The-Ant-Lab/arcobaleno/firmware/build-ARCOBALENO_PLUS/genhdr/pins.h

extern const pin_obj_t pin_A0_obj;
#define pin_A0 (&pin_A0_obj)
extern const pin_af_obj_t pin_A0_af[];
extern const pin_obj_t pin_A1_obj;
#define pin_A1 (&pin_A1_obj)
extern const pin_af_obj_t pin_A1_af[];
extern const pin_obj_t pin_A2_obj;
#define pin_A2 (&pin_A2_obj)
extern const pin_af_obj_t pin_A2_af[];
extern const pin_obj_t pin_A3_obj;
#define pin_A3 (&pin_A3_obj)
extern const pin_af_obj_t pin_A3_af[];
extern const pin_obj_t pin_A4_obj;
#define pin_A4 (&pin_A4_obj)
extern const pin_af_obj_t pin_A4_af[];
extern const pin_obj_t pin_A5_obj;
#define pin_A5 (&pin_A5_obj)
extern const pin_af_obj_t pin_A5_af[];
extern const pin_obj_t pin_A6_obj;
#define pin_A6 (&pin_A6_obj)
extern const pin_af_obj_t pin_A6_af[];
extern const pin_obj_t pin_A7_obj;
#define pin_A7 (&pin_A7_obj)
extern const pin_af_obj_t pin_A7_af[];
extern const pin_obj_t pin_A8_obj;
#define pin_A8 (&pin_A8_obj)
extern const pin_af_obj_t pin_A8_af[];
extern const pin_obj_t pin_A9_obj;
#define pin_A9 (&pin_A9_obj)
extern const pin_af_obj_t pin_A9_af[];
extern const pin_obj_t pin_A10_obj;
#define pin_A10 (&pin_A10_obj)
extern const pin_af_obj_t pin_A10_af[];
extern const pin_obj_t pin_A11_obj;
#define pin_A11 (&pin_A11_obj)
extern const pin_af_obj_t pin_A11_af[];
extern const pin_obj_t pin_A12_obj;
#define pin_A12 (&pin_A12_obj)
extern const pin_af_obj_t pin_A12_af[];
extern const pin_obj_t pin_A15_obj;
#define pin_A15 (&pin_A15_obj)
extern const pin_af_obj_t pin_A15_af[];
extern const pin_obj_t pin_B0_obj;
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
#define pyb_pin_SD_CMD pin_D2
#define pyb_pin_SD_CK pin_C12
#define pyb_pin_SD_SW pin_A15
#define pyb_pin_USB_VBUS pin_A9
#define pyb_pin_USB_DM pin_A11
#define pyb_pin_USB_DP pin_A12
#define pyb_pin_USB_ID pin_A10
#define pyb_pin_OSC32_IN pin_C14
#define pyb_pin_OSC32_OUT pin_C15
