The-Ant-Lab/arcobaleno/firmware/build-ARCOBALENO_PLUS/frozen_content.c

//
// Content for MICROPY_MODULE_FROZEN_STR
//
#include <stdint.h>
const char mp_frozen_str_names[] = {
"\0"};
const uint32_t mp_frozen_str_sizes[] = {
};
const char mp_frozen_str_content[] = {
};
//
// Content for MICROPY_MODULE_FROZEN_MPY
//
#include "py/mpconfig.h"
#include "py/objint.h"
#include "py/objstr.h"
#include "py/emitglue.h"
#include "py/nativeglue.h"

#if MICROPY_OPT_CACHE_MAP_LOOKUP_IN_BYTECODE != 0
#error "incompatible MICROPY_OPT_CACHE_MAP_LOOKUP_IN_BYTECODE"
#endif

#if MICROPY_LONGINT_IMPL != 2
#error "incompatible MICROPY_LONGINT_IMPL"
#endif

#if MPZ_DIG_SIZE != 16
#error "incompatible MPZ_DIG_SIZE"
#endif

#if MICROPY_PY_BUILTINS_FLOAT
typedef struct _mp_obj_float_t {
    mp_obj_base_t base;
    mp_float_t value;
} mp_obj_float_t;
#endif

#if MICROPY_PY_BUILTINS_COMPLEX
typedef struct _mp_obj_complex_t {
    mp_obj_base_t base;
    mp_float_t real;
    mp_float_t imag;
} mp_obj_complex_t;
#endif

enum {
    MP_QSTR_dht_dot_py = MP_QSTRnumber_of,
    MP_QSTR_esp,
    MP_QSTR_DHTBase,
    MP_QSTR_DHT11,
    MP_QSTR_DHT22,
    MP_QSTR_measure,
    MP_QSTR_buf,
    MP_QSTR_humidity,
    MP_QSTR_temperature,
    MP_QSTR_lcd160cr_dot_py,
    MP_QSTR_PORTRAIT,
    MP_QSTR_LANDSCAPE,
    MP_QSTR_PORTRAIT_UPSIDEDOWN,
    MP_QSTR_LANDSCAPE_UPSIDEDOWN,
    MP_QSTR_STARTUP_DECO_NONE,
    MP_QSTR_STARTUP_DECO_MLOGO,
    MP_QSTR_STARTUP_DECO_INFO,
    MP_QSTR__uart_baud_table,
    MP_QSTR_LCD160CR,
    MP_QSTR_pwr,
    MP_QSTR_i2c,
    MP_QSTR_spi,
    MP_QSTR_i2c_addr,
    MP_QSTR__send,
    MP_QSTR__fcmd2,
    MP_QSTR__fcmd2b,
    MP_QSTR__waitfor,
    MP_QSTR_oflush,
    MP_QSTR_iflush,
    MP_QSTR_rgb,
    MP_QSTR_clip_line,
    MP_QSTR_set_power,
    MP_QSTR_set_orient,
    MP_QSTR_set_brightness,
    MP_QSTR_set_i2c_addr,
    MP_QSTR_set_uart_baudrate,
    MP_QSTR_set_startup_deco,
    MP_QSTR_save_to_flash,
    MP_QSTR_set_pixel,
    MP_QSTR_get_pixel,
    MP_QSTR_get_line,
    MP_QSTR_screen_dump,
    MP_QSTR_screen_load,
    MP_QSTR_set_pos,
    MP_QSTR_set_text_color,
    MP_QSTR_set_font,
    MP_QSTR_set_pen,
    MP_QSTR_erase,
    MP_QSTR_dot,
    MP_QSTR_rect_outline,
    MP_QSTR_rect_interior,
    MP_QSTR_dot_no_clip,
    MP_QSTR_rect_no_clip,
    MP_QSTR_rect_outline_no_clip,
    MP_QSTR_rect_interior_no_clip,
    MP_QSTR_line_no_clip,
    MP_QSTR_poly_dot,
    MP_QSTR_poly_line,
    MP_QSTR_touch_config,
    MP_QSTR_is_touched,
    MP_QSTR_get_touch,
    MP_QSTR_set_spi_win,
    MP_QSTR_fast_spi,
    MP_QSTR_show_framebuf,
    MP_QSTR_set_scroll,
    MP_QSTR_set_scroll_win,
    MP_QSTR_set_scroll_win_param,
    MP_QSTR_set_scroll_buf,
    MP_QSTR_jpeg_start,
    MP_QSTR_jpeg_data,
    MP_QSTR_jpeg,
    MP_QSTR_feed_wdt,
    MP_QSTR_X,
    MP_QSTR_Y,
    MP_QSTR_XY,
    MP_QSTR_YX,
    MP_QSTR_4,
    MP_QSTR_C,
    MP_QSTR_buf16,
    MP_QSTR_buf19,
    MP_QSTR_buf1,
    MP_QSTR_array4,
    MP_QSTR__lt_BBBBBB,
    MP_QSTR_w,
    MP_QSTR_h,
    MP_QSTR_cmd,
    MP_QSTR_fmt,
    MP_QSTR_a0,
    MP_QSTR_a1,
    MP_QSTR_a2,
    MP_QSTR_a3,
    MP_QSTR_a4,
    MP_QSTR_n,
    MP_QSTR_g,
    MP_QSTR_c,
    MP_QSTR__lt_BBB,
    MP_QSTR_orient,
    MP_QSTR__lt_BBW,
    MP_QSTR__lt_BBBBH,
    MP_QSTR_x,
    MP_QSTR_y,
    MP_QSTR__lt_BBBB,
    MP_QSTR__lt_BBBBB,
    MP_QSTR__lt_BBHBBB,
    MP_QSTR__lt_BBHH,
    MP_QSTR_fg,
    MP_QSTR_bg,
    MP_QSTR_font,
    MP_QSTR_scale,
    MP_QSTR_bold,
    MP_QSTR_trans,
    MP_QSTR_s,
    MP_QSTR_x1,
    MP_QSTR_y1,
    MP_QSTR_x2,
    MP_QSTR_y2,
    MP_QSTR_calib,
    MP_QSTR_save,
    MP_QSTR_win,
    MP_QSTR_vec,
    MP_QSTR_pat,
    MP_QSTR_color,
    MP_QSTR_param,
    MP_QSTR__lt_BBH,
    MP_QSTR_l,
    MP_QSTR_lcd160cr_test_dot_py,
    MP_QSTR_lcd160cr,
    MP_QSTR_get_lcd,
    MP_QSTR_show_adc,
    MP_QSTR_test_features,
    MP_QSTR_test_mandel,
    MP_QSTR_test_all,
    MP_QSTR_lcd,
    MP_QSTR__percent_4s_colon__space_,
    MP_QSTR_TEMP,
    MP_QSTR_VBAT,
    MP_QSTR__percent_6_dot_3fV,
    MP_QSTR__percent_5_dot_1f_deg_C,
    MP_QSTR_adc,
    MP_QSTR__percent__dot_2f_space_fps,
    MP_QSTR_in_set,
    MP_QSTR_onewire_dot_py,
    MP_QSTR__ow,
    MP_QSTR_OneWireError,
    MP_QSTR_OneWire,
    MP_QSTR_SEARCH_ROM,
    MP_QSTR_MATCH_ROM,
    MP_QSTR_SKIP_ROM,
    MP_QSTR_select_rom,
    MP_QSTR__search_rom,
    MP_QSTR_required,
    MP_QSTR_rom,
    MP_QSTR_l_rom,
    MP_QSTR_diff,
};

extern const qstr_pool_t mp_qstr_const_pool;
const qstr_pool_t mp_qstr_frozen_const_pool = {
    (qstr_pool_t*)&mp_qstr_const_pool, // previous pool
    MP_QSTRnumber_of, // previous pool size
    10, // allocated entries
    154, // used entries
    {
        (const byte*)"\x5a\xdd\x06" "dht.py",
        (const byte*)"\x63\x24\x03" "esp",
        (const byte*)"\x28\x6f\x07" "DHTBase",
        (const byte*)"\x5d\x80\x05" "DHT11",
        (const byte*)"\xfd\x80\x05" "DHT22",
        (const byte*)"\x1d\xae\x07" "measure",
        (const byte*)"\x74\x49\x03" "buf",
        (const byte*)"\x7c\xaf\x08" "humidity",
        (const byte*)"\xe9\xde\x0b" "temperature",
        (const byte*)"\xcf\xa5\x0b" "lcd160cr.py",
        (const byte*)"\xf2\xcd\x08" "PORTRAIT",
        (const byte*)"\xa6\x7b\x09" "LANDSCAPE",
        (const byte*)"\x01\xb5\x13" "PORTRAIT_UPSIDEDOWN",
        (const byte*)"\xd5\x40\x14" "LANDSCAPE_UPSIDEDOWN",
        (const byte*)"\xa7\xaf\x11" "STARTUP_DECO_NONE",
        (const byte*)"\x2b\x04\x12" "STARTUP_DECO_MLOGO",
        (const byte*)"\xc3\x10\x11" "STARTUP_DECO_INFO",
        (const byte*)"\x44\xc8\x10" "_uart_baud_table",
        (const byte*)"\xc8\x0e\x08" "LCD160CR",
        (const byte*)"\x30\x70\x03" "pwr",
        (const byte*)"\x5d\x5f\x03" "i2c",
        (const byte*)"\xcf\x8d\x03" "spi",
        (const byte*)"\x11\x1f\x08" "i2c_addr",
        (const byte*)"\x46\xdc\x05" "_send",
        (const byte*)"\x24\x42\x06" "_fcmd2",
        (const byte*)"\xc6\x86\x07" "_fcmd2b",
        (const byte*)"\xca\x81\x08" "_waitfor",
        (const byte*)"\xce\x08\x06" "oflush",
        (const byte*)"\x08\xd7\x06" "iflush",
        (const byte*)"\xb2\x8a\x03" "rgb",
        (const byte*)"\x22\xd7\x09" "clip_line",
        (const byte*)"\xa7\xfd\x09" "set_power",
        (const byte*)"\xd3\x6a\x0a" "set_orient",
        (const byte*)"\x91\xbe\x0e" "set_brightness",
        (const byte*)"\x8c\xe7\x0c" "set_i2c_addr",
        (const byte*)"\xc5\xd9\x11" "set_uart_baudrate",
        (const byte*)"\x8f\xbe\x10" "set_startup_deco",
        (const byte*)"\x0f\x3f\x0d" "save_to_flash",
        (const byte*)"\xb0\xda\x09" "set_pixel",
        (const byte*)"\xa4\x17\x09" "get_pixel",
        (const byte*)"\x82\x28\x08" "get_line",
        (const byte*)"\x9a\x5d\x0b" "screen_dump",
        (const byte*)"\x10\xea\x0b" "screen_load",
        (const byte*)"\x54\x6d\x07" "set_pos",
        (const byte*)"\x07\xa7\x0e" "set_text_color",
        (const byte*)"\xcb\xd4\x08" "set_font",
        (const byte*)"\x83\x6d\x07" "set_pen",
        (const byte*)"\xe5\x45\x05" "erase",
        (const byte*)"\x3a\x1f\x03" "dot",
        (const byte*)"\xda\x1c\x0c" "rect_outline",
        (const byte*)"\xca\x14\x0d" "rect_interior",
        (const byte*)"\xed\x75\x0b" "dot_no_clip",
        (const byte*)"\x72\x73\x0c" "rect_no_clip",
        (const byte*)"\x8d\x0a\x14" "rect_outline_no_clip",
        (const byte*)"\x9d\x7e\x15" "rect_interior_no_clip",
        (const byte*)"\x5c\x4e\x0c" "line_no_clip",
        (const byte*)"\x6f\x13\x08" "poly_dot",
        (const byte*)"\xfe\x9a\x09" "poly_line",
        (const byte*)"\x15\x99\x0c" "touch_config",
        (const byte*)"\x04\x72\x0a" "is_touched",
        (const byte*)"\x69\xf2\x09" "get_touch",
        (const byte*)"\x9d\x18\x0b" "set_spi_win",
        (const byte*)"\xf0\x3a\x08" "fast_spi",
        (const byte*)"\x75\x65\x0d" "show_framebuf",
        (const byte*)"\x35\xb2\x0a" "set_scroll",
        (const byte*)"\xda\x67\x0e" "set_scroll_win",
        (const byte*)"\x8a\xbd\x14" "set_scroll_win_param",
        (const byte*)"\x1b\x1a\x0e" "set_scroll_buf",
        (const byte*)"\x22\xea\x0a" "jpeg_start",
        (const byte*)"\x52\x10\x09" "jpeg_data",
        (const byte*)"\x7d\xe7\x04" "jpeg",
        (const byte*)"\x3f\x67\x08" "feed_wdt",
        (const byte*)"\xfd\xb5\x01" "X",
        (const byte*)"\xfc\xb5\x01" "Y",
        (const byte*)"\xc4\x75\x02" "XY",
        (const byte*)"\x24\x75\x02" "YX",
        (const byte*)"\x91\xb5\x01" "4",
        (const byte*)"\xe6\xb5\x01" "C",
        (const byte*)"\x53\x70\x05" "buf16",
        (const byte*)"\x5c\x70\x05" "buf19",
        (const byte*)"\xc5\x77\x04" "buf1",
        (const byte*)"\xc8\xc1\x06" "array4",
        (const byte*)"\x19\x0d\x07" "<BBBBBB",
        (const byte*)"\xd2\xb5\x01" "w",
        (const byte*)"\xcd\xb5\x01" "h",
        (const byte*)"\x2f\x4c\x03" "cmd",
        (const byte*)"\x7a\x38\x03" "fmt",
        (const byte*)"\x74\x6e\x02" "a0",
        (const byte*)"\x75\x6e\x02" "a1",
        (const byte*)"\x76\x6e\x02" "a2",
        (const byte*)"\x77\x6e\x02" "a3",
        (const byte*)"\x70\x6e\x02" "a4",
        (const byte*)"\xcb\xb5\x01" "n",
        (const byte*)"\xc2\xb5\x01" "g",
        (const byte*)"\xc6\xb5\x01" "c",
        (const byte*)"\x7b\x8b\x04" "<BBB",
        (const byte*)"\x8e\x81\x06" "orient",
        (const byte*)"\x6e\x8b\x04" "<BBW",
        (const byte*)"\xf1\x4d\x06" "<BBBBH",
        (const byte*)"\xdd\xb5\x01" "x",
        (const byte*)"\xdc\xb5\x01" "y",
        (const byte*)"\x99\xfa\x05" "<BBBB",
        (const byte*)"\xfb\x4d\x06" "<BBBBB",
        (const byte*)"\xd3\xc2\x07" "<BBHBBB",
        (const byte*)"\xd9\xf9\x05" "<BBHH",
        (const byte*)"\x44\x6e\x02" "fg",
        (const byte*)"\xc0\x6e\x02" "bg",
        (const byte*)"\x96\x2b\x04" "font",
        (const byte*)"\x7d\x51\x05" "scale",
        (const byte*)"\x40\x3c\x04" "bold",
        (const byte*)"\x5f\x45\x05" "trans",
        (const byte*)"\xd6\xb5\x01" "s",
        (const byte*)"\x4c\x71\x02" "x1",
        (const byte*)"\x6d\x71\x02" "y1",
        (const byte*)"\x4f\x71\x02" "x2",
        (const byte*)"\x6e\x71\x02" "y2",
        (const byte*)"\xc0\xed\x05" "calib",
        (const byte*)"\xa4\x83\x04" "save",
        (const byte*)"\xb5\x7f\x03" "win",
        (const byte*)"\x75\x7b\x03" "vec",
        (const byte*)"\xe0\x72\x03" "pat",
        (const byte*)"\xd8\x06\x05" "color",
        (const byte*)"\xca\xc8\x05" "param",
        (const byte*)"\x71\x8b\x04" "<BBH",
        (const byte*)"\xc9\xb5\x01" "l",
        (const byte*)"\x46\x96\x10" "lcd160cr_test.py",
        (const byte*)"\xe8\xf0\x08" "lcd160cr",
        (const byte*)"\xc7\x27\x07" "get_lcd",
        (const byte*)"\xdf\x50\x08" "show_adc",
        (const byte*)"\x2b\x6e\x0d" "test_features",
        (const byte*)"\xc3\x88\x0b" "test_mandel",
        (const byte*)"\xad\xc8\x08" "test_all",
        (const byte*)"\xae\x3f\x03" "lcd",
        (const byte*)"\x9d\x48\x05" "%4s: ",
        (const byte*)"\xe9\xd1\x04" "TEMP",
        (const byte*)"\x24\xc4\x04" "VBAT",
        (const byte*)"\x1b\x2a\x06" "%6.3fV",
        (const byte*)"\x7d\x03\x08" "\x25\x35\x2e\x31\x66\xc2\xb0\x43",
        (const byte*)"\x43\x32\x03" "adc",
        (const byte*)"\x7f\x5a\x08" "%.2f fps",
        (const byte*)"\x1f\x11\x06" "in_set",
        (const byte*)"\x0f\xd8\x0a" "onewire.py",
        (const byte*)"\x82\x1f\x03" "_ow",
        (const byte*)"\x50\x5d\x0c" "OneWireError",
        (const byte*)"\x68\xd8\x07" "OneWire",
        (const byte*)"\xa4\x6f\x0a" "SEARCH_ROM",
        (const byte*)"\xb9\x51\x09" "MATCH_ROM",
        (const byte*)"\xcb\x11\x08" "SKIP_ROM",
        (const byte*)"\xe2\x4f\x0a" "select_rom",
        (const byte*)"\xfb\x7e\x0b" "_search_rom",
        (const byte*)"\x2c\x4c\x08" "required",
        (const byte*)"\xb5\x8b\x03" "rom",
        (const byte*)"\x26\xa3\x05" "l_rom",
        (const byte*)"\xc8\xfc\x04" "diff",
    },
};

// frozen bytecode for file dht.py, scope dht__lt_module_gt__DHTBase___init__
STATIC const byte fun_data_dht__lt_module_gt__DHTBase___init__[27] = {
    0x1a, 0x10,
    MP_QSTR___init__ & 0xff, MP_QSTR___init__ >> 8,
    MP_QSTR_dht_dot_py & 0xff, MP_QSTR_dht_dot_py >> 8,
    0x80, 0x0a, 0x25, 0x00,
    0xb1, 
    0xb0, 
    0x18, MP_QSTR_pin & 0xff, MP_QSTR_pin >> 8, 
    0x12, MP_QSTR_bytearray & 0xff, MP_QSTR_bytearray >> 8, 
    0x85, 
    0x34, 0x01, 
    0xb0, 
    0x18, MP_QSTR_buf & 0xff, MP_QSTR_buf >> 8, 
    0x51, 
    0x63, 
};
STATIC const mp_rom_obj_t const_table_data_dht__lt_module_gt__DHTBase___init__[2] = {
    MP_ROM_QSTR(MP_QSTR_self),
    MP_ROM_QSTR(MP_QSTR_pin),
};
STATIC const mp_raw_code_t raw_code_dht__lt_module_gt__DHTBase___init__ = {
    .kind = MP_CODE_BYTECODE,
    .scope_flags = 0x00,
    .n_pos_args = 2,
    .fun_data = fun_data_dht__lt_module_gt__DHTBase___init__,
    .const_table = (mp_uint_t*)const_table_data_dht__lt_module_gt__DHTBase___init__,
    #if MICROPY_PERSISTENT_CODE_SAVE
    .fun_data_len = 27,
    .n_obj = 0,
    .n_raw_code = 0,
    #if MICROPY_PY_SYS_SETTRACE
    .prelude = {
        .n_state = 4,
        .n_exc_stack = 0,
        .scope_flags = 0,
        .n_pos_args = 2,
        .n_kwonly_args = 0,
        .n_def_pos_args = 0,
        .qstr_block_name = MP_QSTR___init__,
        .qstr_source_file = MP_QSTR_dht_dot_py,
        .line_info = fun_data_dht__lt_module_gt__DHTBase___init__ + 0,
        .opcodes = fun_data_dht__lt_module_gt__DHTBase___init__ + 10,
    },
    .line_of_definition = 0,
    #endif
    #if MICROPY_EMIT_MACHINE_CODE
    .prelude_offset = 0,
    .n_qstr = 0,
    .qstr_link = NULL,
    #endif
    #endif
    #if MICROPY_EMIT_MACHINE_CODE
    .type_sig = 0,
    #endif
};

// frozen bytecode for file dht.py, scope dht__lt_module_gt__DHTBase_measure
STATIC const byte fun_data_dht__lt_module_gt__DHTBase_measure[64] = {
    0x21, 0x14,
    MP_QSTR_measure & 0xff, MP_QSTR_measure >> 8,
    MP_QSTR_dht_dot_py & 0xff, MP_QSTR_dht_dot_py >> 8,
    0x80, 0x0e, 0x25, 0x2b, 0x3a, 0x00,
    0xb0, 
    0x13, MP_QSTR_buf & 0xff, MP_QSTR_buf >> 8, 
    0xc1, 
    0x12, MP_QSTR_dht_readinto & 0xff, MP_QSTR_dht_readinto >> 8, 
    0xb0, 
    0x13, MP_QSTR_pin & 0xff, MP_QSTR_pin >> 8, 
    0xb1, 
    0x34, 0x02, 
    0x59, 
    0xb1, 
    0x80, 
    0x55, 
    0xb1, 
    0x81, 
    0x55, 
    0xf2, 
    0xb1, 
    0x82, 
    0x55, 
    0xf2, 
    0xb1, 
    0x83, 
    0x55, 
    0xf2, 
    0x22, 0x81, 0x7f, 
    0xef, 
    0xb1, 
    0x84, 
    0x55, 
    0xdc, 
    0x44, 0x08, 0x80, 
    0x12, MP_QSTR_Exception & 0xff, MP_QSTR_Exception >> 8, 
    0x23, 0x01, 
    0x34, 0x01, 
    0x65, 
    0x51, 
    0x63, 
};
STATIC const mp_obj_str_t const_obj_dht__lt_module_gt__DHTBase_measure_0 = {{&mp_type_str}, 53040, 14, (const byte*)"\x63\x68\x65\x63\x6b\x73\x75\x6d\x20\x65\x72\x72\x6f\x72"};
STATIC const mp_rom_obj_t const_table_data_dht__lt_module_gt__DHTBase_measure[2] = {
    MP_ROM_QSTR(MP_QSTR_self),
    MP_ROM_PTR(&const_obj_dht__lt_module_gt__DHTBase_measure_0),
};
STATIC const mp_raw_code_t raw_code_dht__lt_module_gt__DHTBase_measure = {
    .kind = MP_CODE_BYTECODE,
    .scope_flags = 0x00,
    .n_pos_args = 1,
    .fun_data = fun_data_dht__lt_module_gt__DHTBase_measure,
    .const_table = (mp_uint_t*)const_table_data_dht__lt_module_gt__DHTBase_measure,
    #if MICROPY_PERSISTENT_CODE_SAVE
    .fun_data_len = 64,
    .n_obj = 1,
    .n_raw_code = 0,
    #if MICROPY_PY_SYS_SETTRACE
    .prelude = {
        .n_state = 5,
        .n_exc_stack = 0,
        .scope_flags = 0,
        .n_pos_args = 1,
        .n_kwonly_args = 0,
        .n_def_pos_args = 0,
        .qstr_block_name = MP_QSTR_measure,
        .qstr_source_file = MP_QSTR_dht_dot_py,
        .line_info = fun_data_dht__lt_module_gt__DHTBase_measure + 0,
        .opcodes = fun_data_dht__lt_module_gt__DHTBase_measure + 12,
    },
    .line_of_definition = 0,
    #endif
    #if MICROPY_EMIT_MACHINE_CODE
    .prelude_offset = 0,
    .n_qstr = 0,
    .qstr_link = NULL,
    #endif
    #endif
    #if MICROPY_EMIT_MACHINE_CODE
    .type_sig = 0,
    #endif
};

// frozen bytecode for file dht.py, scope dht__lt_module_gt__DHTBase
STATIC const byte fun_data_dht__lt_module_gt__DHTBase[35] = {
    0x00, 0x12,
    MP_QSTR_DHTBase & 0xff, MP_QSTR_DHTBase >> 8,
    MP_QSTR_dht_dot_py & 0xff, MP_QSTR_dht_dot_py >> 8,
    0x8c, 0x09, 0x65, 0x20, 0x00,
    0x11, MP_QSTR___name__ & 0xff, MP_QSTR___name__ >> 8, 
    0x16, MP_QSTR___module__ & 0xff, MP_QSTR___module__ >> 8, 
    0x10, MP_QSTR_DHTBase & 0xff, MP_QSTR_DHTBase >> 8, 
    0x16, MP_QSTR___qualname__ & 0xff, MP_QSTR___qualname__ >> 8, 
    0x32, 0x00, 
    0x16, MP_QSTR___init__ & 0xff, MP_QSTR___init__ >> 8, 
    0x32, 0x01, 
    0x16, MP_QSTR_measure & 0xff, MP_QSTR_measure >> 8, 
    0x51, 
    0x63, 
};
STATIC const mp_rom_obj_t const_table_data_dht__lt_module_gt__DHTBase[2] = {
    MP_ROM_PTR(&raw_code_dht__lt_module_gt__DHTBase___init__),
    MP_ROM_PTR(&raw_code_dht__lt_module_gt__DHTBase_measure),
};
STATIC const mp_raw_code_t raw_code_dht__lt_module_gt__DHTBase = {
    .kind = MP_CODE_BYTECODE,
    .scope_flags = 0x00,
    .n_pos_args = 0,
    .fun_data = fun_data_dht__lt_module_gt__DHTBase,
    .const_table = (mp_uint_t*)const_table_data_dht__lt_module_gt__DHTBase,
    #if MICROPY_PERSISTENT_CODE_SAVE
    .fun_data_len = 35,
    .n_obj = 0,
    .n_raw_code = 2,
    #if MICROPY_PY_SYS_SETTRACE
    .prelude = {
        .n_state = 1,
        .n_exc_stack = 0,
        .scope_flags = 0,
        .n_pos_args = 0,
        .n_kwonly_args = 0,
        .n_def_pos_args = 0,
        .qstr_block_name = MP_QSTR_DHTBase,
        .qstr_source_file = MP_QSTR_dht_dot_py,
        .line_info = fun_data_dht__lt_module_gt__DHTBase + 0,
        .opcodes = fun_data_dht__lt_module_gt__DHTBase + 11,
    },
    .line_of_definition = 0,
    #endif
    #if MICROPY_EMIT_MACHINE_CODE
    .prelude_offset = 0,
    .n_qstr = 0,
    .qstr_link = NULL,
    #endif
    #endif
    #if MICROPY_EMIT_MACHINE_CODE
    .type_sig = 0,
    #endif
};

// frozen bytecode for file dht.py, scope dht__lt_module_gt__DHT11_humidity
STATIC const byte fun_data_dht__lt_module_gt__DHT11_humidity[16] = {
    0x11, 0x0e,
    MP_QSTR_humidity & 0xff, MP_QSTR_humidity >> 8,
    MP_QSTR_dht_dot_py & 0xff, MP_QSTR_dht_dot_py >> 8,
    0x80, 0x15, 0x00,
    0xb0, 
    0x13, MP_QSTR_buf & 0xff, MP_QSTR_buf >> 8, 
    0x80, 
    0x55, 
    0x63, 
};
STATIC const mp_rom_obj_t const_table_data_dht__lt_module_gt__DHT11_humidity[1] = {
    MP_ROM_QSTR(MP_QSTR_self),
};
STATIC const mp_raw_code_t raw_code_dht__lt_module_gt__DHT11_humidity = {
    .kind = MP_CODE_BYTECODE,
    .scope_flags = 0x00,
    .n_pos_args = 1,
    .fun_data = fun_data_dht__lt_module_gt__DHT11_humidity,
    .const_table = (mp_uint_t*)const_table_data_dht__lt_module_gt__DHT11_humidity,
    #if MICROPY_PERSISTENT_CODE_SAVE
    .fun_data_len = 16,
    .n_obj = 0,
    .n_raw_code = 0,
    #if MICROPY_PY_SYS_SETTRACE
    .prelude = {
        .n_state = 3,
        .n_exc_stack = 0,
        .scope_flags = 0,
        .n_pos_args = 1,
        .n_kwonly_args = 0,
        .n_def_pos_args = 0,
        .qstr_block_name = MP_QSTR_humidity,
        .qstr_source_file = MP_QSTR_dht_dot_py,
        .line_info = fun_data_dht__lt_module_gt__DHT11_humidity + 0,
        .opcodes = fun_data_dht__lt_module_gt__DHT11_humidity + 9,
    },
    .line_of_definition = 0,
    #endif
    #if MICROPY_EMIT_MACHINE_CODE
    .prelude_offset = 0,
    .n_qstr = 0,
    .qstr_link = NULL,
    #endif
    #endif
    #if MICROPY_EMIT_MACHINE_CODE
    .type_sig = 0,
    #endif
};

// frozen bytecode for file dht.py, scope dht__lt_module_gt__DHT11_temperature
STATIC const byte fun_data_dht__lt_module_gt__DHT11_temperature[16] = {
    0x11, 0x0e,
    MP_QSTR_temperature & 0xff, MP_QSTR_temperature >> 8,
    MP_QSTR_dht_dot_py & 0xff, MP_QSTR_dht_dot_py >> 8,
    0x80, 0x18, 0x00,
    0xb0, 
    0x13, MP_QSTR_buf & 0xff, MP_QSTR_buf >> 8, 
    0x82, 
    0x55, 
    0x63, 
};
STATIC const mp_rom_obj_t const_table_data_dht__lt_module_gt__DHT11_temperature[1] = {
    MP_ROM_QSTR(MP_QSTR_self),
};
STATIC const mp_raw_code_t raw_code_dht__lt_module_gt__DHT11_temperature = {
    .kind = MP_CODE_BYTECODE,
    .scope_flags = 0x00,
    .n_pos_args = 1,
    .fun_data = fun_data_dht__lt_module_gt__DHT11_temperature,
    .const_table = (mp_uint_t*)const_table_data_dht__lt_module_gt__DHT11_temperature,
    #if MICROPY_PERSISTENT_CODE_SAVE
    .fun_data_len = 16,
    .n_obj = 0,
    .n_raw_code = 0,
    #if MICROPY_PY_SYS_SETTRACE
    .prelude = {
        .n_state = 3,
        .n_exc_stack = 0,
        .scope_flags = 0,
        .n_pos_args = 1,
        .n_kwonly_args = 0,
        .n_def_pos_args = 0,
        .qstr_block_name = MP_QSTR_temperature,
        .qstr_source_file = MP_QSTR_dht_dot_py,
        .line_info = fun_data_dht__lt_module_gt__DHT11_temperature + 0,
        .opcodes = fun_data_dht__lt_module_gt__DHT11_temperature + 9,
    },
    .line_of_definition = 0,
    #endif
    #if MICROPY_EMIT_MACHINE_CODE
    .prelude_offset = 0,
    .n_qstr = 0,
    .qstr_link = NULL,
    #endif
    #endif
    #if MICROPY_EMIT_MACHINE_CODE
    .type_sig = 0,
    #endif
};

// frozen bytecode for file dht.py, scope dht__lt_module_gt__DHT11
STATIC const byte fun_data_dht__lt_module_gt__DHT11[34] = {
    0x00, 0x10,
    MP_QSTR_DHT11 & 0xff, MP_QSTR_DHT11 >> 8,
    MP_QSTR_dht_dot_py & 0xff, MP_QSTR_dht_dot_py >> 8,
    0x8c, 0x14, 0x65, 0x00,
    0x11, MP_QSTR___name__ & 0xff, MP_QSTR___name__ >> 8, 
    0x16, MP_QSTR___module__ & 0xff, MP_QSTR___module__ >> 8, 
    0x10, MP_QSTR_DHT11 & 0xff, MP_QSTR_DHT11 >> 8, 
    0x16, MP_QSTR___qualname__ & 0xff, MP_QSTR___qualname__ >> 8, 
    0x32, 0x00, 
    0x16, MP_QSTR_humidity & 0xff, MP_QSTR_humidity >> 8, 
    0x32, 0x01, 
    0x16, MP_QSTR_temperature & 0xff, MP_QSTR_temperature >> 8, 
    0x51, 
    0x63, 
};
STATIC const mp_rom_obj_t const_table_data_dht__lt_module_gt__DHT11[2] = {
    MP_ROM_PTR(&raw_code_dht__lt_module_gt__DHT11_humidity),
    MP_ROM_PTR(&raw_code_dht__lt_module_gt__DHT11_temperature),
};
STATIC const mp_raw_code_t raw_code_dht__lt_module_gt__DHT11 = {
    .kind = MP_CODE_BYTECODE,
    .scope_flags = 0x00,
    .n_pos_args = 0,
    .fun_data = fun_data_dht__lt_module_gt__DHT11,
    .const_table = (mp_uint_t*)const_table_data_dht__lt_module_gt__DHT11,
    #if MICROPY_PERSISTENT_CODE_SAVE
    .fun_data_len = 34,
    .n_obj = 0,
    .n_raw_code = 2,
    #if MICROPY_PY_SYS_SETTRACE
    .prelude = {
        .n_state = 1,
        .n_exc_stack = 0,
        .scope_flags = 0,
        .n_pos_args = 0,
        .n_kwonly_args = 0,
        .n_def_pos_args = 0,
        .qstr_block_name = MP_QSTR_DHT11,
        .qstr_source_file = MP_QSTR_dht_dot_py,
        .line_info = fun_data_dht__lt_module_gt__DHT11 + 0,
        .opcodes = fun_data_dht__lt_module_gt__DHT11 + 10,
    },
    .line_of_definition = 0,
    #endif
    #if MICROPY_EMIT_MACHINE_CODE
    .prelude_offset = 0,
    .n_qstr = 0,
    .qstr_link = NULL,
    #endif
    #endif
    #if MICROPY_EMIT_MACHINE_CODE
    .type_sig = 0,
    #endif
};

// frozen bytecode for file dht.py, scope dht__lt_module_gt__DHT22_humidity
STATIC const byte fun_data_dht__lt_module_gt__DHT22_humidity[28] = {
    0x19, 0x0e,
    MP_QSTR_humidity & 0xff, MP_QSTR_humidity >> 8,
    MP_QSTR_dht_dot_py & 0xff, MP_QSTR_dht_dot_py >> 8,
    0x80, 0x1c, 0x00,
    0xb0, 
    0x13, MP_QSTR_buf & 0xff, MP_QSTR_buf >> 8, 
    0x80, 
    0x55, 
    0x88, 
    0xf0, 
    0xb0, 
    0x13, MP_QSTR_buf & 0xff, MP_QSTR_buf >> 8, 
    0x81, 
    0x55, 
    0xed, 
    0x23, 0x01, 
    0xf4, 
    0x63, 
};
#if MICROPY_OBJ_REPR == MICROPY_OBJ_REPR_A || MICROPY_OBJ_REPR == MICROPY_OBJ_REPR_B
STATIC const mp_obj_float_t const_obj_dht__lt_module_gt__DHT22_humidity_0 = {{&mp_type_float}, 0.1};
#endif
STATIC const mp_rom_obj_t const_table_data_dht__lt_module_gt__DHT22_humidity[2] = {
    MP_ROM_QSTR(MP_QSTR_self),
#if MICROPY_OBJ_REPR == MICROPY_OBJ_REPR_A || MICROPY_OBJ_REPR == MICROPY_OBJ_REPR_B
    MP_ROM_PTR(&const_obj_dht__lt_module_gt__DHT22_humidity_0),
#elif MICROPY_OBJ_REPR == MICROPY_OBJ_REPR_C
    (mp_rom_obj_t)(0xbe4cccce),
#elif MICROPY_OBJ_REPR == MICROPY_OBJ_REPR_D
    (mp_rom_obj_t)(0xbfbd99999999999a),
#endif
};
STATIC const mp_raw_code_t raw_code_dht__lt_module_gt__DHT22_humidity = {
    .kind = MP_CODE_BYTECODE,
    .scope_flags = 0x00,
    .n_pos_args = 1,
    .fun_data = fun_data_dht__lt_module_gt__DHT22_humidity,
    .const_table = (mp_uint_t*)const_table_data_dht__lt_module_gt__DHT22_humidity,
    #if MICROPY_PERSISTENT_CODE_SAVE
    .fun_data_len = 28,
    .n_obj = 1,
    .n_raw_code = 0,
    #if MICROPY_PY_SYS_SETTRACE
    .prelude = {
        .n_state = 4,
        .n_exc_stack = 0,
        .scope_flags = 0,
        .n_pos_args = 1,
        .n_kwonly_args = 0,
        .n_def_pos_args = 0,
        .qstr_block_name = MP_QSTR_humidity,
        .qstr_source_file = MP_QSTR_dht_dot_py,
        .line_info = fun_data_dht__lt_module_gt__DHT22_humidity + 0,
        .opcodes = fun_data_dht__lt_module_gt__DHT22_humidity + 9,
    },
    .line_of_definition = 0,
    #endif
    #if MICROPY_EMIT_MACHINE_CODE
    .prelude_offset = 0,
    .n_qstr = 0,
    .qstr_link = NULL,
    #endif
    #endif
    #if MICROPY_EMIT_MACHINE_CODE
    .type_sig = 0,
    #endif
};

// frozen bytecode for file dht.py, scope dht__lt_module_gt__DHT22_temperature
STATIC const byte fun_data_dht__lt_module_gt__DHT22_temperature[53] = {
    0x21, 0x14,
    MP_QSTR_temperature & 0xff, MP_QSTR_temperature >> 8,
    MP_QSTR_dht_dot_py & 0xff, MP_QSTR_dht_dot_py >> 8,
    0x80, 0x1f, 0x37, 0x2d, 0x23, 0x00,
    0xb0, 
    0x13, MP_QSTR_buf & 0xff, MP_QSTR_buf >> 8, 
    0x82, 
    0x55, 
    0x22, 0x80, 0x7f, 
    0xef, 
    0x88, 
    0xf0, 
    0xb0, 
    0x13, MP_QSTR_buf & 0xff, MP_QSTR_buf >> 8, 
    0x83, 
    0x55, 
    0xed, 
    0x23, 0x01, 
    0xf4, 
    0xc1, 
    0xb0, 
    0x13, MP_QSTR_buf & 0xff, MP_QSTR_buf >> 8, 
    0x82, 
    0x55, 
    0x22, 0x81, 0x00, 
    0xef, 
    0x44, 0x03, 0x80, 
    0xb1, 
    0xd1, 
    0xc1, 
    0xb1, 
    0x63, 
};
#if MICROPY_OBJ_REPR == MICROPY_OBJ_REPR_A || MICROPY_OBJ_REPR == MICROPY_OBJ_REPR_B
STATIC const mp_obj_float_t const_obj_dht__lt_module_gt__DHT22_temperature_0 = {{&mp_type_float}, 0.1};
#endif
STATIC const mp_rom_obj_t const_table_data_dht__lt_module_gt__DHT22_temperature[2] = {
    MP_ROM_QSTR(MP_QSTR_self),
#if MICROPY_OBJ_REPR == MICROPY_OBJ_REPR_A || MICROPY_OBJ_REPR == MICROPY_OBJ_REPR_B
    MP_ROM_PTR(&const_obj_dht__lt_module_gt__DHT22_temperature_0),
#elif MICROPY_OBJ_REPR == MICROPY_OBJ_REPR_C
    (mp_rom_obj_t)(0xbe4cccce),
#elif MICROPY_OBJ_REPR == MICROPY_OBJ_REPR_D
    (mp_rom_obj_t)(0xbfbd99999999999a),
#endif
};
STATIC const mp_raw_code_t raw_code_dht__lt_module_gt__DHT22_temperature = {
    .kind = MP_CODE_BYTECODE,
    .scope_flags = 0x00,
    .n_pos_args = 1,
    .fun_data = fun_data_dht__lt_module_gt__DHT22_temperature,
    .const_table = (mp_uint_t*)const_table_data_dht__lt_module_gt__DHT22_temperature,
    #if MICROPY_PERSISTENT_CODE_SAVE
    .fun_data_len = 53,
    .n_obj = 1,
    .n_raw_code = 0,
    #if MICROPY_PY_SYS_SETTRACE
    .prelude = {
        .n_state = 5,
        .n_exc_stack = 0,
        .scope_flags = 0,
        .n_pos_args = 1,
        .n_kwonly_args = 0,
        .n_def_pos_args = 0,
        .qstr_block_name = MP_QSTR_temperature,
        .qstr_source_file = MP_QSTR_dht_dot_py,
        .line_info = fun_data_dht__lt_module_gt__DHT22_temperature + 0,
        .opcodes = fun_data_dht__lt_module_gt__DHT22_temperature + 12,
    },
    .line_of_definition = 0,
    #endif
    #if MICROPY_EMIT_MACHINE_CODE
    .prelude_offset = 0,
    .n_qstr = 0,
    .qstr_link = NULL,
    #endif
    #endif
    #if MICROPY_EMIT_MACHINE_CODE
    .type_sig = 0,
    #endif
};

// frozen bytecode for file dht.py, scope dht__lt_module_gt__DHT22
STATIC const byte fun_data_dht__lt_module_gt__DHT22[34] = {
    0x00, 0x10,
    MP_QSTR_DHT22 & 0xff, MP_QSTR_DHT22 >> 8,
    MP_QSTR_dht_dot_py & 0xff, MP_QSTR_dht_dot_py >> 8,
    0x8c, 0x1b, 0x65, 0x00,
    0x11, MP_QSTR___name__ & 0xff, MP_QSTR___name__ >> 8, 
    0x16, MP_QSTR___module__ & 0xff, MP_QSTR___module__ >> 8, 
    0x10, MP_QSTR_DHT22 & 0xff, MP_QSTR_DHT22 >> 8, 
    0x16, MP_QSTR___qualname__ & 0xff, MP_QSTR___qualname__ >> 8, 
    0x32, 0x00, 
    0x16, MP_QSTR_humidity & 0xff, MP_QSTR_humidity >> 8, 
    0x32, 0x01, 
    0x16, MP_QSTR_temperature & 0xff, MP_QSTR_temperature >> 8, 
    0x51, 
    0x63, 
};
STATIC const mp_rom_obj_t const_table_data_dht__lt_module_gt__DHT22[2] = {
    MP_ROM_PTR(&raw_code_dht__lt_module_gt__DHT22_humidity),
    MP_ROM_PTR(&raw_code_dht__lt_module_gt__DHT22_temperature),
};
STATIC const mp_raw_code_t raw_code_dht__lt_module_gt__DHT22 = {
    .kind = MP_CODE_BYTECODE,
    .scope_flags = 0x00,
    .n_pos_args = 0,
    .fun_data = fun_data_dht__lt_module_gt__DHT22,
    .const_table = (mp_uint_t*)const_table_data_dht__lt_module_gt__DHT22,
    #if MICROPY_PERSISTENT_CODE_SAVE
    .fun_data_len = 34,
    .n_obj = 0,
    .n_raw_code = 2,
    #if MICROPY_PY_SYS_SETTRACE
    .prelude = {
        .n_state = 1,
        .n_exc_stack = 0,
        .scope_flags = 0,
        .n_pos_args = 0,
        .n_kwonly_args = 0,
        .n_def_pos_args = 0,
        .qstr_block_name = MP_QSTR_DHT22,
        .qstr_source_file = MP_QSTR_dht_dot_py,
        .line_info = fun_data_dht__lt_module_gt__DHT22 + 0,
        .opcodes = fun_data_dht__lt_module_gt__DHT22 + 10,
    },
    .line_of_definition = 0,
    #endif
    #if MICROPY_EMIT_MACHINE_CODE
    .prelude_offset = 0,
    .n_qstr = 0,
    .qstr_link = NULL,
    #endif
    #endif
    #if MICROPY_EMIT_MACHINE_CODE
    .type_sig = 0,
    #endif
};

// frozen bytecode for file dht.py, scope dht_<module>
STATIC const byte fun_data_dht__lt_module_gt_[99] = {
    0x24, 0x1a,
    MP_QSTR__lt_module_gt_ & 0xff, MP_QSTR__lt_module_gt_ >> 8,
    MP_QSTR_dht_dot_py & 0xff, MP_QSTR_dht_dot_py >> 8,
    0x60, 0x23, 0x54, 0x54, 0x8b, 0x0b, 0x8e, 0x07, 0x00,
    0x48, 0x13, 0x00, 
    0x80, 
    0x10, MP_QSTR_dht_readinto & 0xff, MP_QSTR_dht_readinto >> 8, 
    0x2a, 0x01, 
    0x1b, MP_QSTR_esp & 0xff, MP_QSTR_esp >> 8, 
    0x1c, MP_QSTR_dht_readinto & 0xff, MP_QSTR_dht_readinto >> 8, 
    0x16, MP_QSTR_dht_readinto & 0xff, MP_QSTR_dht_readinto >> 8, 
    0x59, 
    0x4a, 0x15, 0x00, 
    0x59, 
    0x80, 
    0x10, MP_QSTR_dht_readinto & 0xff, MP_QSTR_dht_readinto >> 8, 
    0x2a, 0x01, 
    0x1b, MP_QSTR_pyb & 0xff, MP_QSTR_pyb >> 8, 
    0x1c, MP_QSTR_dht_readinto & 0xff, MP_QSTR_dht_readinto >> 8, 
    0x16, MP_QSTR_dht_readinto & 0xff, MP_QSTR_dht_readinto >> 8, 
    0x59, 
    0x4a, 0x01, 0x00, 
    0x5d, 
    0x54, 
    0x32, 0x00, 
    0x10, MP_QSTR_DHTBase & 0xff, MP_QSTR_DHTBase >> 8, 
    0x34, 0x02, 
    0x16, MP_QSTR_DHTBase & 0xff, MP_QSTR_DHTBase >> 8, 
    0x54, 
    0x32, 0x01, 
    0x10, MP_QSTR_DHT11 & 0xff, MP_QSTR_DHT11 >> 8, 
    0x11, MP_QSTR_DHTBase & 0xff, MP_QSTR_DHTBase >> 8, 
    0x34, 0x03, 
    0x16, MP_QSTR_DHT11 & 0xff, MP_QSTR_DHT11 >> 8, 
    0x54, 
    0x32, 0x02, 
    0x10, MP_QSTR_DHT22 & 0xff, MP_QSTR_DHT22 >> 8, 
    0x11, MP_QSTR_DHTBase & 0xff, MP_QSTR_DHTBase >> 8, 
    0x34, 0x03, 
    0x16, MP_QSTR_DHT22 & 0xff, MP_QSTR_DHT22 >> 8, 
    0x51, 
    0x63, 
};
STATIC const mp_rom_obj_t const_table_data_dht__lt_module_gt_[3] = {
    MP_ROM_PTR(&raw_code_dht__lt_module_gt__DHTBase),
    MP_ROM_PTR(&raw_code_dht__lt_module_gt__DHT11),
    MP_ROM_PTR(&raw_code_dht__lt_module_gt__DHT22),
};
const mp_raw_code_t raw_code_dht__lt_module_gt_ = {
    .kind = MP_CODE_BYTECODE,
    .scope_flags = 0x00,
    .n_pos_args = 0,
    .fun_data = fun_data_dht__lt_module_gt_,
    .const_table = (mp_uint_t*)const_table_data_dht__lt_module_gt_,
    #if MICROPY_PERSISTENT_CODE_SAVE
    .fun_data_len = 99,
    .n_obj = 0,
    .n_raw_code = 3,
    #if MICROPY_PY_SYS_SETTRACE
    .prelude = {
        .n_state = 5,
        .n_exc_stack = 1,
        .scope_flags = 0,
        .n_pos_args = 0,
        .n_kwonly_args = 0,
        .n_def_pos_args = 0,
        .qstr_block_name = MP_QSTR__lt_module_gt_,
        .qstr_source_file = MP_QSTR_dht_dot_py,
        .line_info = fun_data_dht__lt_module_gt_ + 0,
        .opcodes = fun_data_dht__lt_module_gt_ + 15,
    },
    .line_of_definition = 0,
    #endif
    #if MICROPY_EMIT_MACHINE_CODE
    .prelude_offset = 0,
    .n_qstr = 0,
    .qstr_link = NULL,
    #endif
    #endif
    #if MICROPY_EMIT_MACHINE_CODE
    .type_sig = 0,
    #endif
};

// frozen bytecode for file lcd160cr.py, scope lcd160cr__lt_module_gt__LCD160CR___init__
STATIC const byte fun_data_lcd160cr__lt_module_gt__LCD160CR___init__[390] = {
    0x8a, 0x91, 0x80, 0x88, 0x40, 0x50,
    MP_QSTR___init__ & 0xff, MP_QSTR___init__ >> 8,
    MP_QSTR_lcd160cr_dot_py & 0xff, MP_QSTR_lcd160cr_dot_py >> 8,
    0x80, 0x21, 0x33, 0x24, 0x24, 0x29, 0x28, 0x22, 0x22, 0x47, 0x32, 0x48, 0x26, 0x33, 0x26, 0x32, 0x26, 0x5b, 0x29, 0x25, 0x67, 0x60, 0x25, 0x25, 0x25, 0x65, 0x2a, 0x2a, 0x29, 0x26, 0x3d, 0x2a, 0x6a, 0x28, 0x37, 0x00,
    0xb1, 
    0x10, MP_QSTR_X & 0xff, MP_QSTR_X >> 8, 
    0x10, MP_QSTR_Y & 0xff, MP_QSTR_Y >> 8, 
    0x10, MP_QSTR_XY & 0xff, MP_QSTR_XY >> 8, 
    0x10, MP_QSTR_YX & 0xff, MP_QSTR_YX >> 8, 
    0x2a, 0x04, 
    0xdd, 
    0x44, 0x11, 0x80, 
    0xb1, 
    0x7f, 
    0x55, 
    0xc6, 
    0xb1, 
    0x80, 
    0x55, 
    0xc7, 
    0xb7, 
    0x10, MP_QSTR_4 & 0xff, MP_QSTR_4 >> 8, 
    0xf2, 
    0xc8, 
    0x42, 0x2d, 0x80, 
    0xb1, 
    0x10, MP_QSTR_C & 0xff, MP_QSTR_C >> 8, 
    0xd9, 
    0x44, 0x0b, 0x80, 
    0x82, 
    0xc6, 
    0x82, 
    0xc7, 
    0x10, MP_QSTR_A7 & 0xff, MP_QSTR_A7 >> 8, 
    0xc8, 
    0x42, 0x1a, 0x80, 
    0xb2, 
    0x51, 
    0xde, 
    0x43, 0x0c, 0x80, 
    0xb3, 
    0x51, 
    0xde, 
    0x43, 0x06, 0x80, 
    0xb4, 
    0x51, 
    0xde, 
    0x44, 0x08, 0x80, 
    0x12, MP_QSTR_ValueError & 0xff, MP_QSTR_ValueError >> 8, 
    0x23, 0x06, 
    0x34, 0x01, 
    0x65, 
    0xb2, 
    0x51, 
    0xde, 
    0x44, 0x13, 0x80, 
    0x12, MP_QSTR_machine & 0xff, MP_QSTR_machine >> 8, 
    0x14, MP_QSTR_Pin & 0xff, MP_QSTR_Pin >> 8, 
    0xb8, 
    0x12, MP_QSTR_machine & 0xff, MP_QSTR_machine >> 8, 
    0x13, MP_QSTR_Pin & 0xff, MP_QSTR_Pin >> 8, 
    0x13, MP_QSTR_OUT & 0xff, MP_QSTR_OUT >> 8, 
    0x36, 0x02, 
    0xc2, 
    0xb3, 
    0x51, 
    0xde, 
    0x44, 0x12, 0x80, 
    0x12, MP_QSTR_machine & 0xff, MP_QSTR_machine >> 8, 
    0x14, MP_QSTR_I2C & 0xff, MP_QSTR_I2C >> 8, 
    0xb6, 
    0x10, MP_QSTR_freq & 0xff, MP_QSTR_freq >> 8, 
    0x22, 0xbd, 0x84, 0x40, 
    0x36, 0x82, 0x01, 
    0xc3, 
    0xb4, 
    0x51, 
    0xde, 
    0x44, 0x1b, 0x80, 
    0x12, MP_QSTR_machine & 0xff, MP_QSTR_machine >> 8, 
    0x14, MP_QSTR_SPI & 0xff, MP_QSTR_SPI >> 8, 
    0xb7, 
    0x10, MP_QSTR_baudrate & 0xff, MP_QSTR_baudrate >> 8, 
    0x22, 0x86, 0xb7, 0xfc, 0x60, 
    0x10, MP_QSTR_polarity & 0xff, MP_QSTR_polarity >> 8, 
    0x80, 
    0x10, MP_QSTR_phase & 0xff, MP_QSTR_phase >> 8, 
    0x80, 
    0x36, 0x86, 0x01, 
    0xc4, 
    0xb2, 
    0x14, MP_QSTR_value & 0xff, MP_QSTR_value >> 8, 
    0x36, 0x00, 
    0x43, 0x0c, 0x80, 
    0xb2, 
    0x81, 
    0x34, 0x01, 
    0x59, 
    0x12, MP_QSTR_sleep_ms & 0xff, MP_QSTR_sleep_ms >> 8, 
    0x8a, 
    0x34, 0x01, 
    0x59, 
    0xb2, 
    0xb0, 
    0x18, MP_QSTR_pwr & 0xff, MP_QSTR_pwr >> 8, 
    0xb3, 
    0xb0, 
    0x18, MP_QSTR_i2c & 0xff, MP_QSTR_i2c >> 8, 
    0xb4, 
    0xb0, 
    0x18, MP_QSTR_spi & 0xff, MP_QSTR_spi >> 8, 
    0xb5, 
    0xb0, 
    0x18, MP_QSTR_i2c_addr & 0xff, MP_QSTR_i2c_addr >> 8, 
    0x12, MP_QSTR_bytearray & 0xff, MP_QSTR_bytearray >> 8, 
    0x90, 
    0x34, 0x01, 
    0xb0, 
    0x18, MP_QSTR_buf16 & 0xff, MP_QSTR_buf16 >> 8, 
    0x12, MP_QSTR_bytearray & 0xff, MP_QSTR_bytearray >> 8, 
    0x93, 
    0x34, 0x01, 
    0xb0, 
    0x18, MP_QSTR_buf19 & 0xff, MP_QSTR_buf19 >> 8, 
    0x51, 
    0x2b, 0x01, 
    0x8a, 
    0xf4, 
    0xb0, 
    0x18, MP_QSTR_buf & 0xff, MP_QSTR_buf >> 8, 
    0x81, 
    0x42, 0x18, 0x80, 
    0x57, 
    0xc6, 
    0x12, MP_QSTR_memoryview & 0xff, MP_QSTR_memoryview >> 8, 
    0xb0, 
    0x13, MP_QSTR_buf16 & 0xff, MP_QSTR_buf16 >> 8, 
    0x34, 0x01, 
    0x80, 
    0xb6, 
    0x2e, 0x02, 
    0x55, 
    0xb0, 
    0x13, MP_QSTR_buf & 0xff, MP_QSTR_buf >> 8, 
    0xb6, 
    0x56, 
    0x81, 
    0xe5, 
    0x57, 
    0x8a, 
    0xd7, 
    0x43, 0xe2, 0x7f, 
    0x59, 
    0xb0, 
    0x13, MP_QSTR_buf & 0xff, MP_QSTR_buf >> 8, 
    0x81, 
    0x55, 
    0xb0, 
    0x18, MP_QSTR_buf1 & 0xff, MP_QSTR_buf1 >> 8, 
    0x80, 
    0x80, 
    0x80, 
    0x80, 
    0x2b, 0x04, 
    0xb0, 
    0x18, MP_QSTR_array4 & 0xff, MP_QSTR_array4 >> 8, 
    0xb0, 
    0x14, MP_QSTR_set_orient & 0xff, MP_QSTR_set_orient >> 8, 
    0x80, 
    0x36, 0x01, 
    0x59, 
    0xb0, 
    0x14, MP_QSTR__fcmd2b & 0xff, MP_QSTR__fcmd2b >> 8, 
    0x10, MP_QSTR__lt_BBBBBB & 0xff, MP_QSTR__lt_BBBBBB >> 8, 
    0x22, 0x80, 0x76, 
    0x80, 
    0x80, 
    0xb0, 
    0x13, MP_QSTR_w & 0xff, MP_QSTR_w >> 8, 
    0xb0, 
    0x13, MP_QSTR_h & 0xff, MP_QSTR_h >> 8, 
    0x36, 0x06, 
    0x59, 
    0xb0, 
    0x14, MP_QSTR__fcmd2b & 0xff, MP_QSTR__fcmd2b >> 8, 
    0x10, MP_QSTR__lt_BBBBBB & 0xff, MP_QSTR__lt_BBBBBB >> 8, 
    0x22, 0x80, 0x79, 
    0x80, 
    0x80, 
    0xb0, 
    0x13, MP_QSTR_w & 0xff, MP_QSTR_w >> 8, 
    0xb0, 
    0x13, MP_QSTR_h & 0xff, MP_QSTR_h >> 8, 
    0x36, 0x06, 
    0x59, 
    0x51, 
    0x63, 
};
STATIC const mp_obj_str_t const_obj_lcd160cr__lt_module_gt__LCD160CR___init___0 = {{&mp_type_str}, 26676, 61, (const byte*)"\x6d\x75\x73\x74\x20\x73\x70\x65\x63\x69\x66\x79\x20\x76\x61\x6c\x69\x64\x20\x22\x63\x6f\x6e\x6e\x65\x63\x74\x22\x20\x6f\x72\x20\x61\x6c\x6c\x20\x6f\x66\x20\x22\x70\x77\x72\x22\x2c\x20\x22\x69\x32\x63\x22\x20\x61\x6e\x64\x20\x22\x73\x70\x69\x22"};
STATIC const mp_rom_obj_t const_table_data_lcd160cr__lt_module_gt__LCD160CR___init__[7] = {
    MP_ROM_QSTR(MP_QSTR_self),
    MP_ROM_QSTR(MP_QSTR_connect),
    MP_ROM_QSTR(MP_QSTR_pwr),
    MP_ROM_QSTR(MP_QSTR_i2c),
    MP_ROM_QSTR(MP_QSTR_spi),
    MP_ROM_QSTR(MP_QSTR_i2c_addr),
    MP_ROM_PTR(&const_obj_lcd160cr__lt_module_gt__LCD160CR___init___0),
};
STATIC const mp_raw_code_t raw_code_lcd160cr__lt_module_gt__LCD160CR___init__ = {
    .kind = MP_CODE_BYTECODE,
    .scope_flags = 0x08,
    .n_pos_args = 2,
    .fun_data = fun_data_lcd160cr__lt_module_gt__LCD160CR___init__,
    .const_table = (mp_uint_t*)const_table_data_lcd160cr__lt_module_gt__LCD160CR___init__,
    #if MICROPY_PERSISTENT_CODE_SAVE
    .fun_data_len = 390,
    .n_obj = 1,
    .n_raw_code = 0,
    #if MICROPY_PY_SYS_SETTRACE
    .prelude = {
        .n_state = 18,
        .n_exc_stack = 0,
        .scope_flags = 8,
        .n_pos_args = 2,
        .n_kwonly_args = 4,
        .n_def_pos_args = 1,
        .qstr_block_name = MP_QSTR___init__,
        .qstr_source_file = MP_QSTR_lcd160cr_dot_py,
        .line_info = fun_data_lcd160cr__lt_module_gt__LCD160CR___init__ + 0,
        .opcodes = fun_data_lcd160cr__lt_module_gt__LCD160CR___init__ + 46,
    },
    .line_of_definition = 0,
    #endif
    #if MICROPY_EMIT_MACHINE_CODE
    .prelude_offset = 0,
    .n_qstr = 0,
    .qstr_link = NULL,
    #endif
    #endif
    #if MICROPY_EMIT_MACHINE_CODE
    .type_sig = 0,
    #endif
};

// frozen bytecode for file lcd160cr.py, scope lcd160cr__lt_module_gt__LCD160CR__send
STATIC const byte fun_data_lcd160cr__lt_module_gt__LCD160CR__send[102] = {
    0x52, 0x20,
    MP_QSTR__send & 0xff, MP_QSTR__send >> 8,
    MP_QSTR_lcd160cr_dot_py & 0xff, MP_QSTR_lcd160cr_dot_py >> 8,
    0x80, 0x50, 0x2f, 0x2b, 0x22, 0x27, 0x27, 0x20, 0x36, 0x26, 0x22, 0x00,
    0xb0, 
    0x13, MP_QSTR_i2c & 0xff, MP_QSTR_i2c >> 8, 
    0x14, MP_QSTR_writeto & 0xff, MP_QSTR_writeto >> 8, 
    0xb0, 
    0x13, MP_QSTR_i2c_addr & 0xff, MP_QSTR_i2c_addr >> 8, 
    0xb1, 
    0x36, 0x02, 
    0xc2, 
    0xb2, 
    0x12, MP_QSTR_len & 0xff, MP_QSTR_len >> 8, 
    0xb1, 
    0x34, 0x01, 
    0xd9, 
    0x44, 0x02, 0x80, 
    0x51, 
    0x63, 
    0x12, MP_QSTR_memoryview & 0xff, MP_QSTR_memoryview >> 8, 
    0xb1, 
    0x34, 0x01, 
    0xc1, 
    0x12, MP_QSTR_len & 0xff, MP_QSTR_len >> 8, 
    0xb1, 
    0x34, 0x01, 
    0xc3, 
    0xb2, 
    0xb0, 
    0x13, MP_QSTR_i2c & 0xff, MP_QSTR_i2c >> 8, 
    0x14, MP_QSTR_writeto & 0xff, MP_QSTR_writeto >> 8, 
    0xb0, 
    0x13, MP_QSTR_i2c_addr & 0xff, MP_QSTR_i2c_addr >> 8, 
    0xb1, 
    0xb2, 
    0x51, 
    0x2e, 0x02, 
    0x55, 
    0x36, 0x02, 
    0xe5, 
    0xc2, 
    0xb2, 
    0xb3, 
    0xd9, 
    0x44, 0x02, 0x80, 
    0x51, 
    0x63, 
    0x12, MP_QSTR_sleep_ms & 0xff, MP_QSTR_sleep_ms >> 8, 
    0x8a, 
    0x34, 0x01, 
    0x59, 
    0x42, 0xd8, 0x7f, 
    0x51, 
    0x63, 
};
STATIC const mp_rom_obj_t const_table_data_lcd160cr__lt_module_gt__LCD160CR__send[2] = {
    MP_ROM_QSTR(MP_QSTR_self),
    MP_ROM_QSTR(MP_QSTR_cmd),
};
STATIC const mp_raw_code_t raw_code_lcd160cr__lt_module_gt__LCD160CR__send = {
    .kind = MP_CODE_BYTECODE,
    .scope_flags = 0x00,
    .n_pos_args = 2,
    .fun_data = fun_data_lcd160cr__lt_module_gt__LCD160CR__send,
    .const_table = (mp_uint_t*)const_table_data_lcd160cr__lt_module_gt__LCD160CR__send,
    #if MICROPY_PERSISTENT_CODE_SAVE
    .fun_data_len = 102,
    .n_obj = 0,
    .n_raw_code = 0,
    #if MICROPY_PY_SYS_SETTRACE
    .prelude = {
        .n_state = 11,
        .n_exc_stack = 0,
        .scope_flags = 0,
        .n_pos_args = 2,
        .n_kwonly_args = 0,
        .n_def_pos_args = 0,
        .qstr_block_name = MP_QSTR__send,
        .qstr_source_file = MP_QSTR_lcd160cr_dot_py,
        .line_info = fun_data_lcd160cr__lt_module_gt__LCD160CR__send + 0,
        .opcodes = fun_data_lcd160cr__lt_module_gt__LCD160CR__send + 18,
    },
    .line_of_definition = 0,
    #endif
    #if MICROPY_EMIT_MACHINE_CODE
    .prelude_offset = 0,
    .n_qstr = 0,
    .qstr_link = NULL,
    #endif
    #endif
    #if MICROPY_EMIT_MACHINE_CODE
    .type_sig = 0,
    #endif
};

// frozen bytecode for file lcd160cr.py, scope lcd160cr__lt_module_gt__LCD160CR__fcmd2
STATIC const byte fun_data_lcd160cr__lt_module_gt__LCD160CR__fcmd2[48] = {
    0xe9, 0x84, 0x01, 0x12,
    MP_QSTR__fcmd2 & 0xff, MP_QSTR__fcmd2 >> 8,
    MP_QSTR_lcd160cr_dot_py & 0xff, MP_QSTR_lcd160cr_dot_py >> 8,
    0x80, 0x5c, 0x2c, 0x2d, 0x00,
    0xb0, 
    0x13, MP_QSTR_buf & 0xff, MP_QSTR_buf >> 8, 
    0x12, MP_QSTR_calcsize & 0xff, MP_QSTR_calcsize >> 8, 
    0xb1, 
    0x34, 0x01, 
    0x55, 
    0xc5, 
    0x12, MP_QSTR_pack_into & 0xff, MP_QSTR_pack_into >> 8, 
    0xb1, 
    0xb5, 
    0x80, 
    0x82, 
    0xb2, 
    0xb3, 
    0xb4, 
    0x34, 0x07, 
    0x59, 
    0xb0, 
    0x14, MP_QSTR__send & 0xff, MP_QSTR__send >> 8, 
    0xb5, 
    0x36, 0x01, 
    0x59, 
    0x51, 
    0x63, 
};
STATIC const mp_rom_obj_t const_table_data_lcd160cr__lt_module_gt__LCD160CR__fcmd2[5] = {
    MP_ROM_QSTR(MP_QSTR_self),
    MP_ROM_QSTR(MP_QSTR_fmt),
    MP_ROM_QSTR(MP_QSTR_a0),
    MP_ROM_QSTR(MP_QSTR_a1),
    MP_ROM_QSTR(MP_QSTR_a2),
};
STATIC const mp_raw_code_t raw_code_lcd160cr__lt_module_gt__LCD160CR__fcmd2 = {
    .kind = MP_CODE_BYTECODE,
    .scope_flags = 0x00,
    .n_pos_args = 5,
    .fun_data = fun_data_lcd160cr__lt_module_gt__LCD160CR__fcmd2,
    .const_table = (mp_uint_t*)const_table_data_lcd160cr__lt_module_gt__LCD160CR__fcmd2,
    #if MICROPY_PERSISTENT_CODE_SAVE
    .fun_data_len = 48,
    .n_obj = 0,
    .n_raw_code = 0,
    #if MICROPY_PY_SYS_SETTRACE
    .prelude = {
        .n_state = 14,
        .n_exc_stack = 0,
        .scope_flags = 0,
        .n_pos_args = 5,
        .n_kwonly_args = 0,
        .n_def_pos_args = 2,
        .qstr_block_name = MP_QSTR__fcmd2,
        .qstr_source_file = MP_QSTR_lcd160cr_dot_py,
        .line_info = fun_data_lcd160cr__lt_module_gt__LCD160CR__fcmd2 + 0,
        .opcodes = fun_data_lcd160cr__lt_module_gt__LCD160CR__fcmd2 + 13,
    },
    .line_of_definition = 0,
    #endif
    #if MICROPY_EMIT_MACHINE_CODE
    .prelude_offset = 0,
    .n_qstr = 0,
    .qstr_link = NULL,
    #endif
    #endif
    #if MICROPY_EMIT_MACHINE_CODE
    .type_sig = 0,
    #endif
};

// frozen bytecode for file lcd160cr.py, scope lcd160cr__lt_module_gt__LCD160CR__fcmd2b
STATIC const byte fun_data_lcd160cr__lt_module_gt__LCD160CR__fcmd2b[49] = {
    0x8b, 0x15, 0x12,
    MP_QSTR__fcmd2b & 0xff, MP_QSTR__fcmd2b >> 8,
    MP_QSTR_lcd160cr_dot_py & 0xff, MP_QSTR_lcd160cr_dot_py >> 8,
    0x80, 0x61, 0x2c, 0x2f, 0x00,
    0xb0, 
    0x13, MP_QSTR_buf & 0xff, MP_QSTR_buf >> 8, 
    0x12, MP_QSTR_calcsize & 0xff, MP_QSTR_calcsize >> 8, 
    0xb1, 
    0x34, 0x01, 
    0x55, 
    0xc7, 
    0x12, MP_QSTR_pack_into & 0xff, MP_QSTR_pack_into >> 8, 
    0xb1, 
    0xb7, 
    0x80, 
    0x82, 
    0xb2, 
    0xb3, 
    0xb4, 
    0xb5, 
    0xb6, 
    0x34, 0x09, 
    0x59, 
    0xb0, 
    0x14, MP_QSTR__send & 0xff, MP_QSTR__send >> 8, 
    0xb7, 
    0x36, 0x01, 
    0x59, 
    0x51, 
    0x63, 
};
STATIC const mp_rom_obj_t const_table_data_lcd160cr__lt_module_gt__LCD160CR__fcmd2b[7] = {
    MP_ROM_QSTR(MP_QSTR_self),
    MP_ROM_QSTR(MP_QSTR_fmt),
    MP_ROM_QSTR(MP_QSTR_a0),
    MP_ROM_QSTR(MP_QSTR_a1),
    MP_ROM_QSTR(MP_QSTR_a2),
    MP_ROM_QSTR(MP_QSTR_a3),
    MP_ROM_QSTR(MP_QSTR_a4),
};
STATIC const mp_raw_code_t raw_code_lcd160cr__lt_module_gt__LCD160CR__fcmd2b = {
    .kind = MP_CODE_BYTECODE,
    .scope_flags = 0x00,
    .n_pos_args = 7,
    .fun_data = fun_data_lcd160cr__lt_module_gt__LCD160CR__fcmd2b,
    .const_table = (mp_uint_t*)const_table_data_lcd160cr__lt_module_gt__LCD160CR__fcmd2b,
    #if MICROPY_PERSISTENT_CODE_SAVE
    .fun_data_len = 49,
    .n_obj = 0,
    .n_raw_code = 0,
    #if MICROPY_PY_SYS_SETTRACE
    .prelude = {
        .n_state = 18,
        .n_exc_stack = 0,
        .scope_flags = 0,
        .n_pos_args = 7,
        .n_kwonly_args = 0,
        .n_def_pos_args = 1,
        .qstr_block_name = MP_QSTR__fcmd2b,
        .qstr_source_file = MP_QSTR_lcd160cr_dot_py,
        .line_info = fun_data_lcd160cr__lt_module_gt__LCD160CR__fcmd2b + 0,
        .opcodes = fun_data_lcd160cr__lt_module_gt__LCD160CR__fcmd2b + 12,
    },
    .line_of_definition = 0,
    #endif
    #if MICROPY_EMIT_MACHINE_CODE
    .prelude_offset = 0,
    .n_qstr = 0,
    .qstr_link = NULL,
    #endif
    #endif
    #if MICROPY_EMIT_MACHINE_CODE
    .type_sig = 0,
    #endif
};

// frozen bytecode for file lcd160cr.py, scope lcd160cr__lt_module_gt__LCD160CR__waitfor
STATIC const byte fun_data_lcd160cr__lt_module_gt__LCD160CR__waitfor[99] = {
    0x3b, 0x1e,
    MP_QSTR__waitfor & 0xff, MP_QSTR__waitfor >> 8,
    MP_QSTR_lcd160cr_dot_py & 0xff, MP_QSTR_lcd160cr_dot_py >> 8,
    0x80, 0x66, 0x24, 0x23, 0x32, 0x2b, 0x2f, 0x22, 0x24, 0x2b, 0x00,
    0x22, 0xa7, 0x08, 
    0xc3, 
    0x42, 0x39, 0x80, 
    0xb0, 
    0x13, MP_QSTR_i2c & 0xff, MP_QSTR_i2c >> 8, 
    0x14, MP_QSTR_readfrom_into & 0xff, MP_QSTR_readfrom_into >> 8, 
    0xb0, 
    0x13, MP_QSTR_i2c_addr & 0xff, MP_QSTR_i2c_addr >> 8, 
    0xb0, 
    0x13, MP_QSTR_buf1 & 0xff, MP_QSTR_buf1 >> 8, 
    0x36, 0x02, 
    0x59, 
    0xb0, 
    0x13, MP_QSTR_buf1 & 0xff, MP_QSTR_buf1 >> 8, 
    0x80, 
    0x55, 
    0xb1, 
    0xdb, 
    0x44, 0x11, 0x80, 
    0xb0, 
    0x13, MP_QSTR_i2c & 0xff, MP_QSTR_i2c >> 8, 
    0x14, MP_QSTR_readfrom_into & 0xff, MP_QSTR_readfrom_into >> 8, 
    0xb0, 
    0x13, MP_QSTR_i2c_addr & 0xff, MP_QSTR_i2c_addr >> 8, 
    0xb2, 
    0x36, 0x02, 
    0x59, 
    0x51, 
    0x63, 
    0xb3, 
    0x81, 
    0xe6, 
    0xc3, 
    0x12, MP_QSTR_sleep_ms & 0xff, MP_QSTR_sleep_ms >> 8, 
    0x81, 
    0x34, 0x01, 
    0x59, 
    0xb3, 
    0x43, 0xc3, 0x7f, 
    0x12, MP_QSTR_OSError & 0xff, MP_QSTR_OSError >> 8, 
    0x12, MP_QSTR_uerrno & 0xff, MP_QSTR_uerrno >> 8, 
    0x13, MP_QSTR_ETIMEDOUT & 0xff, MP_QSTR_ETIMEDOUT >> 8, 
    0x34, 0x01, 
    0x65, 
    0x51, 
    0x63, 
};
STATIC const mp_rom_obj_t const_table_data_lcd160cr__lt_module_gt__LCD160CR__waitfor[3] = {
    MP_ROM_QSTR(MP_QSTR_self),
    MP_ROM_QSTR(MP_QSTR_n),
    MP_ROM_QSTR(MP_QSTR_buf),
};
STATIC const mp_raw_code_t raw_code_lcd160cr__lt_module_gt__LCD160CR__waitfor = {
    .kind = MP_CODE_BYTECODE,
    .scope_flags = 0x00,
    .n_pos_args = 3,
    .fun_data = fun_data_lcd160cr__lt_module_gt__LCD160CR__waitfor,
    .const_table = (mp_uint_t*)const_table_data_lcd160cr__lt_module_gt__LCD160CR__waitfor,
    #if MICROPY_PERSISTENT_CODE_SAVE
    .fun_data_len = 99,
    .n_obj = 0,
    .n_raw_code = 0,
    #if MICROPY_PY_SYS_SETTRACE
    .prelude = {
        .n_state = 8,
        .n_exc_stack = 0,
        .scope_flags = 0,
        .n_pos_args = 3,
        .n_kwonly_args = 0,
        .n_def_pos_args = 0,
        .qstr_block_name = MP_QSTR__waitfor,
        .qstr_source_file = MP_QSTR_lcd160cr_dot_py,
        .line_info = fun_data_lcd160cr__lt_module_gt__LCD160CR__waitfor + 0,
        .opcodes = fun_data_lcd160cr__lt_module_gt__LCD160CR__waitfor + 17,
    },
    .line_of_definition = 0,
    #endif
    #if MICROPY_EMIT_MACHINE_CODE
    .prelude_offset = 0,
    .n_qstr = 0,
    .qstr_link = NULL,
    #endif
    #endif
    #if MICROPY_EMIT_MACHINE_CODE
    .type_sig = 0,
    #endif
};

// frozen bytecode for file lcd160cr.py, scope lcd160cr__lt_module_gt__LCD160CR_oflush
STATIC const byte fun_data_lcd160cr__lt_module_gt__LCD160CR_oflush[91] = {
    0xba, 0x01, 0x1e,
    MP_QSTR_oflush & 0xff, MP_QSTR_oflush >> 8,
    MP_QSTR_lcd160cr_dot_py & 0xff, MP_QSTR_lcd160cr_dot_py >> 8,
    0x80, 0x71, 0x24, 0x23, 0x34, 0x27, 0x26, 0x22, 0x24, 0x2d, 0x00,
    0x22, 0xa7, 0x08, 
    0xc2, 
    0x42, 0x30, 0x80, 
    0xb0, 
    0x13, MP_QSTR_i2c & 0xff, MP_QSTR_i2c >> 8, 
    0x14, MP_QSTR_readfrom_into & 0xff, MP_QSTR_readfrom_into >> 8, 
    0xb0, 
    0x13, MP_QSTR_i2c_addr & 0xff, MP_QSTR_i2c_addr >> 8, 
    0x81, 
    0xf2, 
    0xb0, 
    0x13, MP_QSTR_buf1 & 0xff, MP_QSTR_buf1 >> 8, 
    0x36, 0x02, 
    0x59, 
    0xb0, 
    0x13, MP_QSTR_buf1 & 0xff, MP_QSTR_buf1 >> 8, 
    0x80, 
    0x55, 
    0xc3, 
    0xb3, 
    0xb1, 
    0xdb, 
    0x44, 0x02, 0x80, 
    0x51, 
    0x63, 
    0xb2, 
    0x81, 
    0xe6, 
    0xc2, 
    0x12, MP_QSTR_machine & 0xff, MP_QSTR_machine >> 8, 
    0x14, MP_QSTR_idle & 0xff, MP_QSTR_idle >> 8, 
    0x36, 0x00, 
    0x59, 
    0xb2, 
    0x43, 0xcc, 0x7f, 
    0x12, MP_QSTR_OSError & 0xff, MP_QSTR_OSError >> 8, 
    0x12, MP_QSTR_uerrno & 0xff, MP_QSTR_uerrno >> 8, 
    0x13, MP_QSTR_ETIMEDOUT & 0xff, MP_QSTR_ETIMEDOUT >> 8, 
    0x34, 0x01, 
    0x65, 
    0x51, 
    0x63, 
};
STATIC const mp_rom_obj_t const_table_data_lcd160cr__lt_module_gt__LCD160CR_oflush[2] = {
    MP_ROM_QSTR(MP_QSTR_self),
    MP_ROM_QSTR(MP_QSTR_n),
};
STATIC const mp_raw_code_t raw_code_lcd160cr__lt_module_gt__LCD160CR_oflush = {
    .kind = MP_CODE_BYTECODE,
    .scope_flags = 0x00,
    .n_pos_args = 2,
    .fun_data = fun_data_lcd160cr__lt_module_gt__LCD160CR_oflush,
    .const_table = (mp_uint_t*)const_table_data_lcd160cr__lt_module_gt__LCD160CR_oflush,
    #if MICROPY_PERSISTENT_CODE_SAVE
    .fun_data_len = 91,
    .n_obj = 0,
    .n_raw_code = 0,
    #if MICROPY_PY_SYS_SETTRACE
    .prelude = {
        .n_state = 8,
        .n_exc_stack = 0,
        .scope_flags = 0,
        .n_pos_args = 2,
        .n_kwonly_args = 0,
        .n_def_pos_args = 1,
        .qstr_block_name = MP_QSTR_oflush,
        .qstr_source_file = MP_QSTR_lcd160cr_dot_py,
        .line_info = fun_data_lcd160cr__lt_module_gt__LCD160CR_oflush + 0,
        .opcodes = fun_data_lcd160cr__lt_module_gt__LCD160CR_oflush + 18,
    },
    .line_of_definition = 0,
    #endif
    #if MICROPY_EMIT_MACHINE_CODE
    .prelude_offset = 0,
    .n_qstr = 0,
    .qstr_link = NULL,
    #endif
    #endif
    #if MICROPY_EMIT_MACHINE_CODE
    .type_sig = 0,
    #endif
};

// frozen bytecode for file lcd160cr.py, scope lcd160cr__lt_module_gt__LCD160CR_iflush
STATIC const byte fun_data_lcd160cr__lt_module_gt__LCD160CR_iflush[83] = {
    0x29, 0x1c,
    MP_QSTR_iflush & 0xff, MP_QSTR_iflush >> 8,
    MP_QSTR_lcd160cr_dot_py & 0xff, MP_QSTR_lcd160cr_dot_py >> 8,
    0x80, 0x7c, 0x24, 0x23, 0x32, 0x2b, 0x22, 0x24, 0x2b, 0x00,
    0x22, 0xa7, 0x08, 
    0xc1, 
    0x42, 0x2a, 0x80, 
    0xb0, 
    0x13, MP_QSTR_i2c & 0xff, MP_QSTR_i2c >> 8, 
    0x14, MP_QSTR_readfrom_into & 0xff, MP_QSTR_readfrom_into >> 8, 
    0xb0, 
    0x13, MP_QSTR_i2c_addr & 0xff, MP_QSTR_i2c_addr >> 8, 
    0xb0, 
    0x13, MP_QSTR_buf16 & 0xff, MP_QSTR_buf16 >> 8, 
    0x36, 0x02, 
    0x59, 
    0xb0, 
    0x13, MP_QSTR_buf16 & 0xff, MP_QSTR_buf16 >> 8, 
    0x80, 
    0x55, 
    0x80, 
    0xd9, 
    0x44, 0x02, 0x80, 
    0x51, 
    0x63, 
    0xb1, 
    0x81, 
    0xe6, 
    0xc1, 
    0x12, MP_QSTR_sleep_ms & 0xff, MP_QSTR_sleep_ms >> 8, 
    0x81, 
    0x34, 0x01, 
    0x59, 
    0xb1, 
    0x43, 0xd2, 0x7f, 
    0x12, MP_QSTR_OSError & 0xff, MP_QSTR_OSError >> 8, 
    0x12, MP_QSTR_uerrno & 0xff, MP_QSTR_uerrno >> 8, 
    0x13, MP_QSTR_ETIMEDOUT & 0xff, MP_QSTR_ETIMEDOUT >> 8, 
    0x34, 0x01, 
    0x65, 
    0x51, 
    0x63, 
};
STATIC const mp_rom_obj_t const_table_data_lcd160cr__lt_module_gt__LCD160CR_iflush[1] = {
    MP_ROM_QSTR(MP_QSTR_self),
};
STATIC const mp_raw_code_t raw_code_lcd160cr__lt_module_gt__LCD160CR_iflush = {
    .kind = MP_CODE_BYTECODE,
    .scope_flags = 0x00,
    .n_pos_args = 1,
    .fun_data = fun_data_lcd160cr__lt_module_gt__LCD160CR_iflush,
    .const_table = (mp_uint_t*)const_table_data_lcd160cr__lt_module_gt__LCD160CR_iflush,
    #if MICROPY_PERSISTENT_CODE_SAVE
    .fun_data_len = 83,
    .n_obj = 0,
    .n_raw_code = 0,
    #if MICROPY_PY_SYS_SETTRACE
    .prelude = {
        .n_state = 6,
        .n_exc_stack = 0,
        .scope_flags = 0,
        .n_pos_args = 1,
        .n_kwonly_args = 0,
        .n_def_pos_args = 0,
        .qstr_block_name = MP_QSTR_iflush,
        .qstr_source_file = MP_QSTR_lcd160cr_dot_py,
        .line_info = fun_data_lcd160cr__lt_module_gt__LCD160CR_iflush + 0,
        .opcodes = fun_data_lcd160cr__lt_module_gt__LCD160CR_iflush + 16,
    },
    .line_of_definition = 0,
    #endif
    #if MICROPY_EMIT_MACHINE_CODE
    .prelude_offset = 0,
    .n_qstr = 0,
    .qstr_link = NULL,
    #endif
    #endif
    #if MICROPY_EMIT_MACHINE_CODE
    .type_sig = 0,
    #endif
};

// frozen bytecode for file lcd160cr.py, scope lcd160cr__lt_module_gt__LCD160CR_rgb
STATIC const byte fun_data_lcd160cr__lt_module_gt__LCD160CR_rgb[29] = {
    0x2b, 0x0e,
    MP_QSTR_rgb & 0xff, MP_QSTR_rgb >> 8,
    MP_QSTR_lcd160cr_dot_py & 0xff, MP_QSTR_lcd160cr_dot_py >> 8,
    0x80, 0x89, 0x00,
    0xb2, 
    0x22, 0x81, 0x78, 
    0xef, 
    0x88, 
    0xf0, 
    0xb1, 
    0x22, 0x81, 0x7c, 
    0xef, 
    0x83, 
    0xf0, 
    0xed, 
    0xb0, 
    0x83, 
    0xf1, 
    0xed, 
    0x63, 
};
STATIC const mp_rom_obj_t const_table_data_lcd160cr__lt_module_gt__LCD160CR_rgb[3] = {
    MP_ROM_QSTR(MP_QSTR_r),
    MP_ROM_QSTR(MP_QSTR_g),
    MP_ROM_QSTR(MP_QSTR_b),
};
STATIC const mp_raw_code_t raw_code_lcd160cr__lt_module_gt__LCD160CR_rgb = {
    .kind = MP_CODE_BYTECODE,
    .scope_flags = 0x00,
    .n_pos_args = 3,
    .fun_data = fun_data_lcd160cr__lt_module_gt__LCD160CR_rgb,
    .const_table = (mp_uint_t*)const_table_data_lcd160cr__lt_module_gt__LCD160CR_rgb,
    #if MICROPY_PERSISTENT_CODE_SAVE
    .fun_data_len = 29,
    .n_obj = 0,
    .n_raw_code = 0,
    #if MICROPY_PY_SYS_SETTRACE
    .prelude = {
        .n_state = 6,
        .n_exc_stack = 0,
        .scope_flags = 0,
        .n_pos_args = 3,
        .n_kwonly_args = 0,
        .n_def_pos_args = 0,
        .qstr_block_name = MP_QSTR_rgb,
        .qstr_source_file = MP_QSTR_lcd160cr_dot_py,
        .line_info = fun_data_lcd160cr__lt_module_gt__LCD160CR_rgb + 0,
        .opcodes = fun_data_lcd160cr__lt_module_gt__LCD160CR_rgb + 9,
    },
    .line_of_definition = 0,
    #endif
    #if MICROPY_EMIT_MACHINE_CODE
    .prelude_offset = 0,
    .n_qstr = 0,
    .qstr_link = NULL,
    #endif
    #endif
    #if MICROPY_EMIT_MACHINE_CODE
    .type_sig = 0,
    #endif
};

// frozen bytecode for file lcd160cr.py, scope lcd160cr__lt_module_gt__LCD160CR_clip_line
STATIC const byte fun_data_lcd160cr__lt_module_gt__LCD160CR_clip_line[599] = {
    0x5b, 0x7c,
    MP_QSTR_clip_line & 0xff, MP_QSTR_clip_line >> 8,
    MP_QSTR_lcd160cr_dot_py & 0xff, MP_QSTR_lcd160cr_dot_py >> 8,
    0x80, 0x8d, 0x20, 0x24, 0x28, 0x27, 0x28, 0x27, 0x28, 0x27, 0x28, 0x27, 0x28, 0x27, 0x28, 0x27, 0x28, 0x27, 0x28, 0x27, 0x26, 0x22, 0x26, 0x24, 0x26, 0x2a, 0x2d, 0x2d, 0x3b, 0x27, 0x26, 0x2a, 0x2d, 0x2d, 0x3e, 0x29, 0x26, 0x2a, 0x28, 0x26, 0x28, 0x49, 0x2a, 0x2d, 0x2d, 0x3e, 0x49, 0x2a, 0x28, 0x24, 0x28, 0x47, 0x2a, 0x2d, 0x2d, 0x3b, 0x47, 0x00,
    0x80, 
    0x57, 
    0xc3, 
    0xc4, 
    0xb0, 
    0x81, 
    0x55, 
    0x80, 
    0xd7, 
    0x44, 0x07, 0x80, 
    0xb3, 
    0x88, 
    0xe0, 
    0xc3, 
    0x42, 0x0f, 0x80, 
    0xb0, 
    0x81, 
    0x55, 
    0xb2, 
    0xd8, 
    0x44, 0x07, 0x80, 
    0xb3, 
    0x84, 
    0xe0, 
    0xc3, 
    0x42, 0x00, 0x80, 
    0xb0, 
    0x80, 
    0x55, 
    0x80, 
    0xd7, 
    0x44, 0x07, 0x80, 
    0xb3, 
    0x81, 
    0xe0, 
    0xc3, 
    0x42, 0x0f, 0x80, 
    0xb0, 
    0x80, 
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
};
STATIC const mp_rom_obj_t const_table_data_lcd160cr__lt_module_gt__LCD160CR_clip_line[3] = {
    MP_ROM_QSTR(MP_QSTR_c),
    MP_ROM_QSTR(MP_QSTR_w),
    MP_ROM_QSTR(MP_QSTR_h),
};
STATIC const mp_raw_code_t raw_code_lcd160cr__lt_module_gt__LCD160CR_clip_line = {
    .kind = MP_CODE_BYTECODE,
    .scope_flags = 0x00,
    .n_pos_args = 3,
    .fun_data = fun_data_lcd160cr__lt_module_gt__LCD160CR_clip_line,
    .const_table = (mp_uint_t*)const_table_data_lcd160cr__lt_module_gt__LCD160CR_clip_line,
    #if MICROPY_PERSISTENT_CODE_SAVE
    .fun_data_len = 599,
    .n_obj = 0,
    .n_raw_code = 0,
    #if MICROPY_PY_SYS_SETTRACE
    .prelude = {
        .n_state = 12,
        .n_exc_stack = 0,
        .scope_flags = 0,
        .n_pos_args = 3,
        .n_kwonly_args = 0,
        .n_def_pos_args = 0,
        .qstr_block_name = MP_QSTR_clip_line,
        .qstr_source_file = MP_QSTR_lcd160cr_dot_py,
        .line_info = fun_data_lcd160cr__lt_module_gt__LCD160CR_clip_line + 0,
        .opcodes = fun_data_lcd160cr__lt_module_gt__LCD160CR_clip_line + 64,
    },
    .line_of_definition = 0,
    #endif
    #if MICROPY_EMIT_MACHINE_CODE
    .prelude_offset = 0,
    .n_qstr = 0,
    .qstr_link = NULL,
    #endif
    #endif
    #if MICROPY_EMIT_MACHINE_CODE
    .type_sig = 0,
    #endif
};

// frozen bytecode for file lcd160cr.py, scope lcd160cr__lt_module_gt__LCD160CR_set_power
STATIC const byte fun_data_lcd160cr__lt_module_gt__LCD160CR_set_power[27] = {
    0x22, 0x10,
    MP_QSTR_set_power & 0xff, MP_QSTR_set_power >> 8,
    MP_QSTR_lcd160cr_dot_py & 0xff, MP_QSTR_lcd160cr_dot_py >> 8,
    0x80, 0xcd, 0x28, 0x00,
    0xb0, 
    0x14, MP_QSTR_pwr & 0xff, MP_QSTR_pwr >> 8, 
    0xb1, 
    0x36, 0x01, 
    0x59, 
    0x12, MP_QSTR_sleep_ms & 0xff, MP_QSTR_sleep_ms >> 8, 
    0x8f, 
    0x34, 0x01, 
    0x59, 
    0x51, 
    0x63, 
};
STATIC const mp_rom_obj_t const_table_data_lcd160cr__lt_module_gt__LCD160CR_set_power[2] = {
    MP_ROM_QSTR(MP_QSTR_self),
    MP_ROM_QSTR(MP_QSTR_on),
};
STATIC const mp_raw_code_t raw_code_lcd160cr__lt_module_gt__LCD160CR_set_power = {
    .kind = MP_CODE_BYTECODE,
    .scope_flags = 0x00,
    .n_pos_args = 2,
    .fun_data = fun_data_lcd160cr__lt_module_gt__LCD160CR_set_power,
    .const_table = (mp_uint_t*)const_table_data_lcd160cr__lt_module_gt__LCD160CR_set_power,
    #if MICROPY_PERSISTENT_CODE_SAVE
    .fun_data_len = 27,
    .n_obj = 0,
    .n_raw_code = 0,
    #if MICROPY_PY_SYS_SETTRACE
    .prelude = {
        .n_state = 5,
        .n_exc_stack = 0,
        .scope_flags = 0,
        .n_pos_args = 2,
        .n_kwonly_args = 0,
        .n_def_pos_args = 0,
        .qstr_block_name = MP_QSTR_set_power,
        .qstr_source_file = MP_QSTR_lcd160cr_dot_py,
        .line_info = fun_data_lcd160cr__lt_module_gt__LCD160CR_set_power + 0,
        .opcodes = fun_data_lcd160cr__lt_module_gt__LCD160CR_set_power + 10,
    },
    .line_of_definition = 0,
    #endif
    #if MICROPY_EMIT_MACHINE_CODE
    .prelude_offset = 0,
    .n_qstr = 0,
    .qstr_link = NULL,
    #endif
    #endif
    #if MICROPY_EMIT_MACHINE_CODE
    .type_sig = 0,
    #endif
};

// frozen bytecode for file lcd160cr.py, scope lcd160cr__lt_module_gt__LCD160CR_set_orient
STATIC const byte fun_data_lcd160cr__lt_module_gt__LCD160CR_set_orient[86] = {
    0x3a, 0x18,
    MP_QSTR_set_orient & 0xff, MP_QSTR_set_orient >> 8,
    MP_QSTR_lcd160cr_dot_py & 0xff, MP_QSTR_lcd160cr_dot_py >> 8,
    0x80, 0xd1, 0x50, 0x27, 0x29, 0x2e, 0x2c, 0x00,
    0xb0, 
    0x14, MP_QSTR__fcmd2 & 0xff, MP_QSTR__fcmd2 >> 8, 
    0x10, MP_QSTR__lt_BBB & 0xff, MP_QSTR__lt_BBB >> 8, 
    0x94, 
    0xb1, 
    0x83, 
    0xef, 
    0x84, 
    0xf2, 
    0x36, 0x03, 
    0x59, 
    0xb0, 
    0x14, MP_QSTR_iflush & 0xff, MP_QSTR_iflush >> 8, 
    0x36, 0x00, 
    0x59, 
    0xb0, 
    0x14, MP_QSTR__send & 0xff, MP_QSTR__send >> 8, 
    0x23, 0x02, 
    0x36, 0x01, 
    0x59, 
    0xb0, 
    0x14, MP_QSTR__waitfor & 0xff, MP_QSTR__waitfor >> 8, 
    0x84, 
    0xb0, 
    0x13, MP_QSTR_buf & 0xff, MP_QSTR_buf >> 8, 
    0x85, 
    0x55, 
    0x36, 0x02, 
    0x59, 
    0xb0, 
    0x13, MP_QSTR_buf & 0xff, MP_QSTR_buf >> 8, 
    0x85, 
    0x55, 
    0x81, 
    0x55, 
    0xb0, 
    0x18, MP_QSTR_w & 0xff, MP_QSTR_w >> 8, 
    0xb0, 
    0x13, MP_QSTR_buf & 0xff, MP_QSTR_buf >> 8, 
    0x85, 
    0x55, 
    0x82, 
    0x55, 
    0xb0, 
    0x18, MP_QSTR_h & 0xff, MP_QSTR_h >> 8, 
    0x51, 
    0x63, 
};
STATIC const mp_obj_str_t const_obj_lcd160cr__lt_module_gt__LCD160CR_set_orient_0 = {{&mp_type_bytes}, 50896, 3, (const byte*)"\x02\x67\x30"};
STATIC const mp_rom_obj_t const_table_data_lcd160cr__lt_module_gt__LCD160CR_set_orient[3] = {
    MP_ROM_QSTR(MP_QSTR_self),
    MP_ROM_QSTR(MP_QSTR_orient),
    MP_ROM_PTR(&const_obj_lcd160cr__lt_module_gt__LCD160CR_set_orient_0),
};
STATIC const mp_raw_code_t raw_code_lcd160cr__lt_module_gt__LCD160CR_set_orient = {
    .kind = MP_CODE_BYTECODE,
    .scope_flags = 0x00,
    .n_pos_args = 2,
    .fun_data = fun_data_lcd160cr__lt_module_gt__LCD160CR_set_orient,
    .const_table = (mp_uint_t*)const_table_data_lcd160cr__lt_module_gt__LCD160CR_set_orient,
    #if MICROPY_PERSISTENT_CODE_SAVE
    .fun_data_len = 86,
    .n_obj = 1,
    .n_raw_code = 0,
    #if MICROPY_PY_SYS_SETTRACE
    .prelude = {
        .n_state = 8,
        .n_exc_stack = 0,
        .scope_flags = 0,
        .n_pos_args = 2,
        .n_kwonly_args = 0,
        .n_def_pos_args = 0,
        .qstr_block_name = MP_QSTR_set_orient,
        .qstr_source_file = MP_QSTR_lcd160cr_dot_py,
        .line_info = fun_data_lcd160cr__lt_module_gt__LCD160CR_set_orient + 0,
        .opcodes = fun_data_lcd160cr__lt_module_gt__LCD160CR_set_orient + 14,
    },
    .line_of_definition = 0,
    #endif
    #if MICROPY_EMIT_MACHINE_CODE
    .prelude_offset = 0,
    .n_qstr = 0,
    .qstr_link = NULL,
    #endif
    #endif
    #if MICROPY_EMIT_MACHINE_CODE
    .type_sig = 0,
    #endif
};

// frozen bytecode for file lcd160cr.py, scope lcd160cr__lt_module_gt__LCD160CR_set_brightness
STATIC const byte fun_data_lcd160cr__lt_module_gt__LCD160CR_set_brightness[23] = {
    0x32, 0x0e,
    MP_QSTR_set_brightness & 0xff, MP_QSTR_set_brightness >> 8,
    MP_QSTR_lcd160cr_dot_py & 0xff, MP_QSTR_lcd160cr_dot_py >> 8,
    0x80, 0xda, 0x00,
    0xb0, 
    0x14, MP_QSTR__fcmd2 & 0xff, MP_QSTR__fcmd2 >> 8, 
    0x10, MP_QSTR__lt_BBB & 0xff, MP_QSTR__lt_BBB >> 8, 
    0x96, 
    0xb1, 
    0x36, 0x03, 
    0x59, 
    0x51, 
    0x63, 
};
STATIC const mp_rom_obj_t const_table_data_lcd160cr__lt_module_gt__LCD160CR_set_brightness[2] = {
    MP_ROM_QSTR(MP_QSTR_self),
    MP_ROM_QSTR(MP_QSTR_value),
};
STATIC const mp_raw_code_t raw_code_lcd160cr__lt_module_gt__LCD160CR_set_brightness = {
    .kind = MP_CODE_BYTECODE,
    .scope_flags = 0x00,
    .n_pos_args = 2,
    .fun_data = fun_data_lcd160cr__lt_module_gt__LCD160CR_set_brightness,
    .const_table = (mp_uint_t*)const_table_data_lcd160cr__lt_module_gt__LCD160CR_set_brightness,
    #if MICROPY_PERSISTENT_CODE_SAVE
    .fun_data_len = 23,
    .n_obj = 0,
    .n_raw_code = 0,
    #if MICROPY_PY_SYS_SETTRACE
    .prelude = {
        .n_state = 7,
        .n_exc_stack = 0,
        .scope_flags = 0,
        .n_pos_args = 2,
        .n_kwonly_args = 0,
        .n_def_pos_args = 0,
        .qstr_block_name = MP_QSTR_set_brightness,
        .qstr_source_file = MP_QSTR_lcd160cr_dot_py,
        .line_info = fun_data_lcd160cr__lt_module_gt__LCD160CR_set_brightness + 0,
        .opcodes = fun_data_lcd160cr__lt_module_gt__LCD160CR_set_brightness + 9,
    },
    .line_of_definition = 0,
    #endif
    #if MICROPY_EMIT_MACHINE_CODE
    .prelude_offset = 0,
    .n_qstr = 0,
    .qstr_link = NULL,
    #endif
    #endif
    #if MICROPY_EMIT_MACHINE_CODE
    .type_sig = 0,
    #endif
};

// frozen bytecode for file lcd160cr.py, scope lcd160cr__lt_module_gt__LCD160CR_set_i2c_addr
STATIC const byte fun_data_lcd160cr__lt_module_gt__LCD160CR_set_i2c_addr[47] = {
    0x42, 0x12,
    MP_QSTR_set_i2c_addr & 0xff, MP_QSTR_set_i2c_addr >> 8,
    MP_QSTR_lcd160cr_dot_py & 0xff, MP_QSTR_lcd160cr_dot_py >> 8,
    0x80, 0xde, 0x26, 0x28, 0x00,
    0xb1, 
    0x83, 
    0xef, 
    0x44, 0x08, 0x80, 
    0x12, MP_QSTR_ValueError & 0xff, MP_QSTR_ValueError >> 8, 
    0x23, 0x02, 
    0x34, 0x01, 
    0x65, 
    0xb0, 
    0x14, MP_QSTR__fcmd2 & 0xff, MP_QSTR__fcmd2 >> 8, 
    0x10, MP_QSTR__lt_BBW & 0xff, MP_QSTR__lt_BBW >> 8, 
    0x8e, 
    0x22, 0x82, 0x8c, 0xe4, 0x49, 
    0xb1, 
    0x98, 
    0xf0, 
    0xed, 
    0x36, 0x03, 
    0x59, 
    0x51, 
    0x63, 
};
STATIC const mp_obj_str_t const_obj_lcd160cr__lt_module_gt__LCD160CR_set_i2c_addr_0 = {{&mp_type_str}, 21473, 34, (const byte*)"\x6d\x75\x73\x74\x20\x73\x70\x65\x63\x69\x66\x79\x20\x6d\x6f\x64\x20\x34\x20\x61\x6c\x69\x67\x6e\x65\x64\x20\x61\x64\x64\x72\x65\x73\x73"};
STATIC const mp_rom_obj_t const_table_data_lcd160cr__lt_module_gt__LCD160CR_set_i2c_addr[3] = {
    MP_ROM_QSTR(MP_QSTR_self),
    MP_ROM_QSTR(MP_QSTR_addr),
    MP_ROM_PTR(&const_obj_lcd160cr__lt_module_gt__LCD160CR_set_i2c_addr_0),
};
STATIC const mp_raw_code_t raw_code_lcd160cr__lt_module_gt__LCD160CR_set_i2c_addr = {
    .kind = MP_CODE_BYTECODE,
    .scope_flags = 0x00,
    .n_pos_args = 2,
    .fun_data = fun_data_lcd160cr__lt_module_gt__LCD160CR_set_i2c_addr,
    .const_table = (mp_uint_t*)const_table_data_lcd160cr__lt_module_gt__LCD160CR_set_i2c_addr,
    #if MICROPY_PERSISTENT_CODE_SAVE
    .fun_data_len = 47,
    .n_obj = 1,
    .n_raw_code = 0,
    #if MICROPY_PY_SYS_SETTRACE
    .prelude = {
        .n_state = 9,
        .n_exc_stack = 0,
        .scope_flags = 0,
        .n_pos_args = 2,
        .n_kwonly_args = 0,
        .n_def_pos_args = 0,
        .qstr_block_name = MP_QSTR_set_i2c_addr,
        .qstr_source_file = MP_QSTR_lcd160cr_dot_py,
        .line_info = fun_data_lcd160cr__lt_module_gt__LCD160CR_set_i2c_addr + 0,
        .opcodes = fun_data_lcd160cr__lt_module_gt__LCD160CR_set_i2c_addr + 11,
    },
    .line_of_definition = 0,
    #endif
    #if MICROPY_EMIT_MACHINE_CODE
    .prelude_offset = 0,
    .n_qstr = 0,
    .qstr_link = NULL,
    #endif
    #endif
    #if MICROPY_EMIT_MACHINE_CODE
    .type_sig = 0,
    #endif
};

// frozen bytecode for file lcd160cr.py, scope lcd160cr__lt_module_gt__LCD160CR_set_uart_baudrate
STATIC const byte fun_data_lcd160cr__lt_module_gt__LCD160CR_set_uart_baudrate[59] = {
    0x3e, 0x14,
    MP_QSTR_set_uart_baudrate & 0xff, MP_QSTR_set_uart_baudrate >> 8,
    MP_QSTR_lcd160cr_dot_py & 0xff, MP_QSTR_lcd160cr_dot_py >> 8,
    0x80, 0xe3, 0x23, 0x52, 0x2c, 0x00,
    0x48, 0x09, 0x00, 
    0x12, MP_QSTR__uart_baud_table & 0xff, MP_QSTR__uart_baud_table >> 8, 
    0xb1, 
    0x55, 
    0xc1, 
    0x4a, 0x15, 0x00, 
    0x57, 
    0x12, MP_QSTR_KeyError & 0xff, MP_QSTR_KeyError >> 8, 
    0xdf, 
    0x44, 0x0c, 0x80, 
    0x59, 
    0x12, MP_QSTR_ValueError & 0xff, MP_QSTR_ValueError >> 8, 
    0x23, 0x02, 
    0x34, 0x01, 
    0x65, 
    0x4a, 0x01, 0x00, 
    0x5d, 
    0xb0, 
    0x14, MP_QSTR__fcmd2 & 0xff, MP_QSTR__fcmd2 >> 8, 
    0x10, MP_QSTR__lt_BBB & 0xff, MP_QSTR__lt_BBB >> 8, 
    0x98, 
    0xb1, 
    0x36, 0x03, 
    0x59, 
    0x51, 
    0x63, 
};
STATIC const mp_obj_str_t const_obj_lcd160cr__lt_module_gt__LCD160CR_set_uart_baudrate_0 = {{&mp_type_str}, 2756, 16, (const byte*)"\x69\x6e\x76\x61\x6c\x69\x64\x20\x62\x61\x75\x64\x72\x61\x74\x65"};
STATIC const mp_rom_obj_t const_table_data_lcd160cr__lt_module_gt__LCD160CR_set_uart_baudrate[3] = {
    MP_ROM_QSTR(MP_QSTR_self),
    MP_ROM_QSTR(MP_QSTR_baudrate),
    MP_ROM_PTR(&const_obj_lcd160cr__lt_module_gt__LCD160CR_set_uart_baudrate_0),
};
STATIC const mp_raw_code_t raw_code_lcd160cr__lt_module_gt__LCD160CR_set_uart_baudrate = {
    .kind = MP_CODE_BYTECODE,
    .scope_flags = 0x00,
    .n_pos_args = 2,
    .fun_data = fun_data_lcd160cr__lt_module_gt__LCD160CR_set_uart_baudrate,
    .const_table = (mp_uint_t*)const_table_data_lcd160cr__lt_module_gt__LCD160CR_set_uart_baudrate,
    #if MICROPY_PERSISTENT_CODE_SAVE
    .fun_data_len = 59,
    .n_obj = 1,
    .n_raw_code = 0,
    #if MICROPY_PY_SYS_SETTRACE
    .prelude = {
        .n_state = 8,
        .n_exc_stack = 1,
        .scope_flags = 0,
        .n_pos_args = 2,
        .n_kwonly_args = 0,
        .n_def_pos_args = 0,
        .qstr_block_name = MP_QSTR_set_uart_baudrate,
        .qstr_source_file = MP_QSTR_lcd160cr_dot_py,
        .line_info = fun_data_lcd160cr__lt_module_gt__LCD160CR_set_uart_baudrate + 0,
        .opcodes = fun_data_lcd160cr__lt_module_gt__LCD160CR_set_uart_baudrate + 12,
    },
    .line_of_definition = 0,
    #endif
    #if MICROPY_EMIT_MACHINE_CODE
    .prelude_offset = 0,
    .n_qstr = 0,
    .qstr_link = NULL,
    #endif
    #endif
    #if MICROPY_EMIT_MACHINE_CODE
    .type_sig = 0,
    #endif
};

// frozen bytecode for file lcd160cr.py, scope lcd160cr__lt_module_gt__LCD160CR_set_startup_deco
STATIC const byte fun_data_lcd160cr__lt_module_gt__LCD160CR_set_startup_deco[23] = {
    0x32, 0x0e,
    MP_QSTR_set_startup_deco & 0xff, MP_QSTR_set_startup_deco >> 8,
    MP_QSTR_lcd160cr_dot_py & 0xff, MP_QSTR_lcd160cr_dot_py >> 8,
    0x80, 0xea, 0x00,
    0xb0, 
    0x14, MP_QSTR__fcmd2 & 0xff, MP_QSTR__fcmd2 >> 8, 
    0x10, MP_QSTR__lt_BBB & 0xff, MP_QSTR__lt_BBB >> 8, 
    0x99, 
    0xb1, 
    0x36, 0x03, 
    0x59, 
    0x51, 
    0x63, 
};
STATIC const mp_rom_obj_t const_table_data_lcd160cr__lt_module_gt__LCD160CR_set_startup_deco[2] = {
    MP_ROM_QSTR(MP_QSTR_self),
    MP_ROM_QSTR(MP_QSTR_value),
};
STATIC const mp_raw_code_t raw_code_lcd160cr__lt_module_gt__LCD160CR_set_startup_deco = {
    .kind = MP_CODE_BYTECODE,
    .scope_flags = 0x00,
    .n_pos_args = 2,
    .fun_data = fun_data_lcd160cr__lt_module_gt__LCD160CR_set_startup_deco,
    .const_table = (mp_uint_t*)const_table_data_lcd160cr__lt_module_gt__LCD160CR_set_startup_deco,
    #if MICROPY_PERSISTENT_CODE_SAVE
    .fun_data_len = 23,
    .n_obj = 0,
    .n_raw_code = 0,
    #if MICROPY_PY_SYS_SETTRACE
    .prelude = {
        .n_state = 7,
        .n_exc_stack = 0,
        .scope_flags = 0,
        .n_pos_args = 2,
        .n_kwonly_args = 0,
        .n_def_pos_args = 0,
        .qstr_block_name = MP_QSTR_set_startup_deco,
        .qstr_source_file = MP_QSTR_lcd160cr_dot_py,
        .line_info = fun_data_lcd160cr__lt_module_gt__LCD160CR_set_startup_deco + 0,
        .opcodes = fun_data_lcd160cr__lt_module_gt__LCD160CR_set_startup_deco + 9,
    },
    .line_of_definition = 0,
    #endif
    #if MICROPY_EMIT_MACHINE_CODE
    .prelude_offset = 0,
    .n_qstr = 0,
    .qstr_link = NULL,
    #endif
    #endif
    #if MICROPY_EMIT_MACHINE_CODE
    .type_sig = 0,
    #endif
};

// frozen bytecode for file lcd160cr.py, scope lcd160cr__lt_module_gt__LCD160CR_save_to_flash
STATIC const byte fun_data_lcd160cr__lt_module_gt__LCD160CR_save_to_flash[20] = {
    0x19, 0x0e,
    MP_QSTR_save_to_flash & 0xff, MP_QSTR_save_to_flash >> 8,
    MP_QSTR_lcd160cr_dot_py & 0xff, MP_QSTR_lcd160cr_dot_py >> 8,
    0x80, 0xed, 0x00,
    0xb0, 
    0x14, MP_QSTR__send & 0xff, MP_QSTR__send >> 8, 
    0x23, 0x01, 
    0x36, 0x01, 
    0x59, 
    0x51, 
    0x63, 
};
STATIC const mp_obj_str_t const_obj_lcd160cr__lt_module_gt__LCD160CR_save_to_flash_0 = {{&mp_type_bytes}, 51055, 3, (const byte*)"\x02\x66\x6e"};
STATIC const mp_rom_obj_t const_table_data_lcd160cr__lt_module_gt__LCD160CR_save_to_flash[2] = {
    MP_ROM_QSTR(MP_QSTR_self),
    MP_ROM_PTR(&const_obj_lcd160cr__lt_module_gt__LCD160CR_save_to_flash_0),
};
STATIC const mp_raw_code_t raw_code_lcd160cr__lt_module_gt__LCD160CR_save_to_flash = {
    .kind = MP_CODE_BYTECODE,
    .scope_flags = 0x00,
    .n_pos_args = 1,
    .fun_data = fun_data_lcd160cr__lt_module_gt__LCD160CR_save_to_flash,
    .const_table = (mp_uint_t*)const_table_data_lcd160cr__lt_module_gt__LCD160CR_save_to_flash,
    #if MICROPY_PERSISTENT_CODE_SAVE
    .fun_data_len = 20,
    .n_obj = 1,
    .n_raw_code = 0,
    #if MICROPY_PY_SYS_SETTRACE
    .prelude = {
        .n_state = 4,
        .n_exc_stack = 0,
        .scope_flags = 0,
        .n_pos_args = 1,
        .n_kwonly_args = 0,
        .n_def_pos_args = 0,
        .qstr_block_name = MP_QSTR_save_to_flash,
        .qstr_source_file = MP_QSTR_lcd160cr_dot_py,
        .line_info = fun_data_lcd160cr__lt_module_gt__LCD160CR_save_to_flash + 0,
        .opcodes = fun_data_lcd160cr__lt_module_gt__LCD160CR_save_to_flash + 9,
    },
    .line_of_definition = 0,
    #endif
    #if MICROPY_EMIT_MACHINE_CODE
    .prelude_offset = 0,
    .n_qstr = 0,
    .qstr_link = NULL,
    #endif
    #endif
    #if MICROPY_EMIT_MACHINE_CODE
    .type_sig = 0,
    #endif
};

// frozen bytecode for file lcd160cr.py, scope lcd160cr__lt_module_gt__LCD160CR_set_pixel
STATIC const byte fun_data_lcd160cr__lt_module_gt__LCD160CR_set_pixel[28] = {
    0xd0, 0x04, 0x0e,
    MP_QSTR_set_pixel & 0xff, MP_QSTR_set_pixel >> 8,
    MP_QSTR_lcd160cr_dot_py & 0xff, MP_QSTR_lcd160cr_dot_py >> 8,
    0x80, 0xf2, 0x00,
    0xb0, 
    0x14, MP_QSTR__fcmd2b & 0xff, MP_QSTR__fcmd2b >> 8, 
    0x10, MP_QSTR__lt_BBBBH & 0xff, MP_QSTR__lt_BBBBH >> 8, 
    0x22, 0x80, 0x41, 
    0xb1, 
    0xb2, 
    0xb3, 
    0x36, 0x05, 
    0x59, 
    0x51, 
    0x63, 
};
STATIC const mp_rom_obj_t const_table_data_lcd160cr__lt_module_gt__LCD160CR_set_pixel[4] = {
    MP_ROM_QSTR(MP_QSTR_self),
    MP_ROM_QSTR(MP_QSTR_x),
    MP_ROM_QSTR(MP_QSTR_y),
    MP_ROM_QSTR(MP_QSTR_c),
};
STATIC const mp_raw_code_t raw_code_lcd160cr__lt_module_gt__LCD160CR_set_pixel = {
    .kind = MP_CODE_BYTECODE,
    .scope_flags = 0x00,
    .n_pos_args = 4,
    .fun_data = fun_data_lcd160cr__lt_module_gt__LCD160CR_set_pixel,
    .const_table = (mp_uint_t*)const_table_data_lcd160cr__lt_module_gt__LCD160CR_set_pixel,
    #if MICROPY_PERSISTENT_CODE_SAVE
    .fun_data_len = 28,
    .n_obj = 0,
    .n_raw_code = 0,
    #if MICROPY_PY_SYS_SETTRACE
    .prelude = {
        .n_state = 11,
        .n_exc_stack = 0,
        .scope_flags = 0,
        .n_pos_args = 4,
        .n_kwonly_args = 0,
        .n_def_pos_args = 0,
        .qstr_block_name = MP_QSTR_set_pixel,
        .qstr_source_file = MP_QSTR_lcd160cr_dot_py,
        .line_info = fun_data_lcd160cr__lt_module_gt__LCD160CR_set_pixel + 0,
        .opcodes = fun_data_lcd160cr__lt_module_gt__LCD160CR_set_pixel + 10,
    },
    .line_of_definition = 0,
    #endif
    #if MICROPY_EMIT_MACHINE_CODE
    .prelude_offset = 0,
    .n_qstr = 0,
    .qstr_link = NULL,
    #endif
    #endif
    #if MICROPY_EMIT_MACHINE_CODE
    .type_sig = 0,
    #endif
};

// frozen bytecode for file lcd160cr.py, scope lcd160cr__lt_module_gt__LCD160CR_get_pixel
STATIC const byte fun_data_lcd160cr__lt_module_gt__LCD160CR_get_pixel[138] = {
    0x4b, 0x20,
    MP_QSTR_get_pixel & 0xff, MP_QSTR_get_pixel >> 8,
    MP_QSTR_lcd160cr_dot_py & 0xff, MP_QSTR_lcd160cr_dot_py >> 8,
    0x80, 0xf5, 0x2f, 0x24, 0x23, 0x32, 0x2b, 0x34, 0x34, 0x24, 0x2b, 0x00,
    0xb0, 
    0x14, MP_QSTR__fcmd2 & 0xff, MP_QSTR__fcmd2 >> 8, 
    0x10, MP_QSTR__lt_BBBB & 0xff, MP_QSTR__lt_BBBB >> 8, 
    0x22, 0x80, 0x61, 
    0xb1, 
    0xb2, 
    0x36, 0x04, 
    0x59, 
    0x22, 0x87, 0x68, 
    0xc3, 
    0x42, 0x50, 0x80, 
    0xb0, 
    0x13, MP_QSTR_i2c & 0xff, MP_QSTR_i2c >> 8, 
    0x14, MP_QSTR_readfrom_into & 0xff, MP_QSTR_readfrom_into >> 8, 
    0xb0, 
    0x13, MP_QSTR_i2c_addr & 0xff, MP_QSTR_i2c_addr >> 8, 
    0xb0, 
    0x13, MP_QSTR_buf1 & 0xff, MP_QSTR_buf1 >> 8, 
    0x36, 0x02, 
    0x59, 
    0xb0, 
    0x13, MP_QSTR_buf1 & 0xff, MP_QSTR_buf1 >> 8, 
    0x80, 
    0x55, 
    0x82, 
    0xdb, 
    0x44, 0x28, 0x80, 
    0xb0, 
    0x13, MP_QSTR_i2c & 0xff, MP_QSTR_i2c >> 8, 
    0x14, MP_QSTR_readfrom_into & 0xff, MP_QSTR_readfrom_into >> 8, 
    0xb0, 
    0x13, MP_QSTR_i2c_addr & 0xff, MP_QSTR_i2c_addr >> 8, 
    0xb0, 
    0x13, MP_QSTR_buf & 0xff, MP_QSTR_buf >> 8, 
    0x83, 
    0x55, 
    0x36, 0x02, 
    0x59, 
    0xb0, 
    0x13, MP_QSTR_buf & 0xff, MP_QSTR_buf >> 8, 
    0x83, 
    0x55, 
    0x81, 
    0x55, 
    0xb0, 
    0x13, MP_QSTR_buf & 0xff, MP_QSTR_buf >> 8, 
    0x83, 
    0x55, 
    0x82, 
    0x55, 
    0x88, 
    0xf0, 
    0xed, 
    0x63, 
    0xb3, 
    0x81, 
    0xe6, 
    0xc3, 
    0x12, MP_QSTR_sleep_ms & 0xff, MP_QSTR_sleep_ms >> 8, 
    0x81, 
    0x34, 0x01, 
    0x59, 
    0xb3, 
    0x43, 0xac, 0x7f, 
    0x12, MP_QSTR_OSError & 0xff, MP_QSTR_OSError >> 8, 
    0x12, MP_QSTR_uerrno & 0xff, MP_QSTR_uerrno >> 8, 
    0x13, MP_QSTR_ETIMEDOUT & 0xff, MP_QSTR_ETIMEDOUT >> 8, 
    0x34, 0x01, 
    0x65, 
    0x51, 
    0x63, 
};
STATIC const mp_rom_obj_t const_table_data_lcd160cr__lt_module_gt__LCD160CR_get_pixel[3] = {
    MP_ROM_QSTR(MP_QSTR_self),
    MP_ROM_QSTR(MP_QSTR_x),
    MP_ROM_QSTR(MP_QSTR_y),
};
STATIC const mp_raw_code_t raw_code_lcd160cr__lt_module_gt__LCD160CR_get_pixel = {
    .kind = MP_CODE_BYTECODE,
    .scope_flags = 0x00,
    .n_pos_args = 3,
    .fun_data = fun_data_lcd160cr__lt_module_gt__LCD160CR_get_pixel,
    .const_table = (mp_uint_t*)const_table_data_lcd160cr__lt_module_gt__LCD160CR_get_pixel,
    #if MICROPY_PERSISTENT_CODE_SAVE
    .fun_data_len = 138,
    .n_obj = 0,
    .n_raw_code = 0,
    #if MICROPY_PY_SYS_SETTRACE
    .prelude = {
        .n_state = 10,
        .n_exc_stack = 0,
        .scope_flags = 0,
        .n_pos_args = 3,
        .n_kwonly_args = 0,
        .n_def_pos_args = 0,
        .qstr_block_name = MP_QSTR_get_pixel,
        .qstr_source_file = MP_QSTR_lcd160cr_dot_py,
        .line_info = fun_data_lcd160cr__lt_module_gt__LCD160CR_get_pixel + 0,
        .opcodes = fun_data_lcd160cr__lt_module_gt__LCD160CR_get_pixel + 18,
    },
    .line_of_definition = 0,
    #endif
    #if MICROPY_EMIT_MACHINE_CODE
    .prelude_offset = 0,
    .n_qstr = 0,
    .qstr_link = NULL,
    #endif
    #endif
    #if MICROPY_EMIT_MACHINE_CODE
    .type_sig = 0,
    #endif
};

// frozen bytecode for file lcd160cr.py, scope lcd160cr__lt_module_gt__LCD160CR_get_line
STATIC const byte fun_data_lcd160cr__lt_module_gt__LCD160CR_get_line[130] = {
    0xe0, 0x04, 0x24,
    MP_QSTR_get_line & 0xff, MP_QSTR_get_line >> 8,
    MP_QSTR_lcd160cr_dot_py & 0xff, MP_QSTR_lcd160cr_dot_py >> 8,
    0x90, 0x01, 0x29, 0x2e, 0x24, 0x24, 0x23, 0x32, 0x2b, 0x2f, 0x22, 0x24, 0x2b, 0x00,
    0x12, MP_QSTR_len & 0xff, MP_QSTR_len >> 8, 
    0xb3, 
    0x34, 0x01, 
    0x82, 
    0xf6, 
    0xc4, 
    0xb0, 
    0x14, MP_QSTR__fcmd2b & 0xff, MP_QSTR__fcmd2b >> 8, 
    0x10, MP_QSTR__lt_BBBBB & 0xff, MP_QSTR__lt_BBBBB >> 8, 
    0x90, 
    0xb4, 
    0xb1, 
    0xb2, 
    0x36, 0x05, 
    0x59, 
    0xb4, 
    0x82, 
    0xe7, 
    0xc4, 
    0x22, 0x87, 0x68, 
    0xc5, 
    0x42, 0x39, 0x80, 
    0xb0, 
    0x13, MP_QSTR_i2c & 0xff, MP_QSTR_i2c >> 8, 
    0x14, MP_QSTR_readfrom_into & 0xff, MP_QSTR_readfrom_into >> 8, 
    0xb0, 
    0x13, MP_QSTR_i2c_addr & 0xff, MP_QSTR_i2c_addr >> 8, 
    0xb0, 
    0x13, MP_QSTR_buf1 & 0xff, MP_QSTR_buf1 >> 8, 
    0x36, 0x02, 
    0x59, 
    0xb0, 
    0x13, MP_QSTR_buf1 & 0xff, MP_QSTR_buf1 >> 8, 
    0x80, 
    0x55, 
    0xb4, 
    0xdb, 
    0x44, 0x11, 0x80, 
    0xb0, 
    0x13, MP_QSTR_i2c & 0xff, MP_QSTR_i2c >> 8, 
    0x14, MP_QSTR_readfrom_into & 0xff, MP_QSTR_readfrom_into >> 8, 
    0xb0, 
    0x13, MP_QSTR_i2c_addr & 0xff, MP_QSTR_i2c_addr >> 8, 
    0xb3, 
    0x36, 0x02, 
    0x59, 
    0x51, 
    0x63, 
    0xb5, 
    0x81, 
    0xe6, 
    0xc5, 
    0x12, MP_QSTR_sleep_ms & 0xff, MP_QSTR_sleep_ms >> 8, 
    0x81, 
    0x34, 0x01, 
    0x59, 
    0xb5, 
    0x43, 0xc3, 0x7f, 
    0x12, MP_QSTR_OSError & 0xff, MP_QSTR_OSError >> 8, 
    0x12, MP_QSTR_uerrno & 0xff, MP_QSTR_uerrno >> 8, 
    0x13, MP_QSTR_ETIMEDOUT & 0xff, MP_QSTR_ETIMEDOUT >> 8, 
    0x34, 0x01, 
    0x65, 
    0x51, 
    0x63, 
};
STATIC const mp_rom_obj_t const_table_data_lcd160cr__lt_module_gt__LCD160CR_get_line[4] = {
    MP_ROM_QSTR(MP_QSTR_self),
    MP_ROM_QSTR(MP_QSTR_x),
    MP_ROM_QSTR(MP_QSTR_y),
    MP_ROM_QSTR(MP_QSTR_buf),
};
STATIC const mp_raw_code_t raw_code_lcd160cr__lt_module_gt__LCD160CR_get_line = {
    .kind = MP_CODE_BYTECODE,
    .scope_flags = 0x00,
    .n_pos_args = 4,
    .fun_data = fun_data_lcd160cr__lt_module_gt__LCD160CR_get_line,
    .const_table = (mp_uint_t*)const_table_data_lcd160cr__lt_module_gt__LCD160CR_get_line,
    #if MICROPY_PERSISTENT_CODE_SAVE
    .fun_data_len = 130,
    .n_obj = 0,
    .n_raw_code = 0,
    #if MICROPY_PY_SYS_SETTRACE
    .prelude = {
        .n_state = 13,
        .n_exc_stack = 0,
        .scope_flags = 0,
        .n_pos_args = 4,
        .n_kwonly_args = 0,
        .n_def_pos_args = 0,
        .qstr_block_name = MP_QSTR_get_line,
        .qstr_source_file = MP_QSTR_lcd160cr_dot_py,
        .line_info = fun_data_lcd160cr__lt_module_gt__LCD160CR_get_line + 0,
        .opcodes = fun_data_lcd160cr__lt_module_gt__LCD160CR_get_line + 21,
    },
    .line_of_definition = 0,
    #endif
    #if MICROPY_EMIT_MACHINE_CODE
    .prelude_offset = 0,
    .n_qstr = 0,
    .qstr_link = NULL,
    #endif
    #endif
    #if MICROPY_EMIT_MACHINE_CODE
    .type_sig = 0,
    #endif
};

// frozen bytecode for file lcd160cr.py, scope lcd160cr__lt_module_gt__LCD160CR_screen_dump
STATIC const byte fun_data_lcd160cr__lt_module_gt__LCD160CR_screen_dump[259] = {
    0x92, 0x94, 0x80, 0x01, 0x32,
    MP_QSTR_screen_dump & 0xff, MP_QSTR_screen_dump >> 8,
    MP_QSTR_lcd160cr_dot_py & 0xff, MP_QSTR_lcd160cr_dot_py >> 8,
    0x90, 0x0f, 0x26, 0x27, 0x26, 0x27, 0x28, 0x2b, 0x65, 0x26, 0x2b, 0x32, 0x36, 0x26, 0x2c, 0x3a, 0x2b, 0x24, 0x2e, 0x3a, 0x00,
    0xb4, 
    0x51, 
    0xde, 
    0x44, 0x07, 0x80, 
    0xb0, 
    0x13, MP_QSTR_w & 0xff, MP_QSTR_w >> 8, 
    0xb2, 
    0xf3, 
    0xc4, 
    0xb5, 
    0x51, 
    0xde, 
    0x44, 0x07, 0x80, 
    0xb0, 
    0x13, MP_QSTR_h & 0xff, MP_QSTR_h >> 8, 
    0xb3, 
    0xf3, 
    0xc5, 
    0xb4, 
    0x22, 0x80, 0x7f, 
    0xda, 
    0x44, 0x10, 0x80, 
    0x12, MP_QSTR_bytearray & 0xff, MP_QSTR_bytearray >> 8, 
    0x82, 
    0xb4, 
    0xf4, 
    0x81, 
    0xf2, 
    0x34, 0x01, 
    0xc6, 
    0x51, 
    0xc7, 
    0x42, 0x23, 0x80, 
    0xb4, 
    0x81, 
    0xf2, 
    0x82, 
    0xf6, 
    0xc8, 
    0x12, MP_QSTR_bytearray & 0xff, MP_QSTR_bytearray >> 8, 
    0x82, 
    0xb8, 
    0xf4, 
    0x81, 
    0xf2, 
    0x34, 0x01, 
    0xc6, 
    0x12, MP_QSTR_memoryview & 0xff, MP_QSTR_memoryview >> 8, 
    0xb6, 
    0x34, 0x01, 
    0x51, 
    0x82, 
    0xb4, 
    0xb8, 
    0xf3, 
    0xf4, 
    0x81, 
    0xf2, 
    0x2e, 0x02, 
    0x55, 
    0xc7, 
    0x12, MP_QSTR_min & 0xff, MP_QSTR_min >> 8, 
    0x12, MP_QSTR_len & 0xff, MP_QSTR_len >> 8, 
    0xb1, 
    0x34, 0x01, 
    0x82, 
    0xb4, 
    0xf4, 
    0xf6, 
    0xb5, 
    0x34, 0x02, 
    0x80, 
    0x42, 0x72, 0x80, 
    0x57, 
    0xc9, 
    0xb9, 
    0xb4, 
    0xf4, 
    0x82, 
    0xf4, 
    0xca, 
    0xb0, 
    0x14, MP_QSTR_get_line & 0xff, MP_QSTR_get_line >> 8, 
    0xb2, 
    0xb3, 
    0xb9, 
    0xf2, 
    0xb6, 
    0x36, 0x03, 
    0x59, 
    0x12, MP_QSTR_memoryview & 0xff, MP_QSTR_memoryview >> 8, 
    0xb6, 
    0x34, 0x01, 
    0x81, 
    0x51, 
    0x2e, 0x02, 
    0x55, 
    0xb1, 
    0xba, 
    0xba, 
    0x12, MP_QSTR_len & 0xff, MP_QSTR_len >> 8, 
    0xb6, 
    0x34, 0x01, 
    0xf2, 
    0x81, 
    0xf3, 
    0x2e, 0x02, 
    0x56, 
    0xba, 
    0x12, MP_QSTR_len & 0xff, MP_QSTR_len >> 8, 
    0xb6, 
    0x34, 0x01, 
    0x81, 
    0xf3, 
    0xe5, 
    0xca, 
    0xb7, 
    0x44, 0x33, 0x80, 
    0xb0, 
    0x14, MP_QSTR_get_line & 0xff, MP_QSTR_get_line >> 8, 
    0xb2, 
    0xb8, 
    0xf2, 
    0xb3, 
    0xb9, 
    0xf2, 
    0xb7, 
    0x36, 0x03, 
    0x59, 
    0x12, MP_QSTR_memoryview & 0xff, MP_QSTR_memoryview >> 8, 
    0xb7, 
    0x34, 0x01, 
    0x81, 
    0x51, 
    0x2e, 0x02, 
    0x55, 
    0xb1, 
    0xba, 
    0xba, 
    0x12, MP_QSTR_len & 0xff, MP_QSTR_len >> 8, 
    0xb7, 
    0x34, 0x01, 
    0xf2, 
    0x81, 
    0xf3, 
    0x2e, 0x02, 
    0x56, 
    0xba, 
    0x12, MP_QSTR_len & 0xff, MP_QSTR_len >> 8, 
    0xb7, 
    0x34, 0x01, 
    0x81, 
    0xf3, 
    0xe5, 
    0xca, 
    0x81, 
    0xe5, 
    0x58, 
    0x5a, 
    0xd7, 
    0x43, 0x88, 0x7f, 
    0x59, 
    0x59, 
    0x51, 
    0x63, 
};
STATIC const mp_rom_obj_t const_table_data_lcd160cr__lt_module_gt__LCD160CR_screen_dump[6] = {
    MP_ROM_QSTR(MP_QSTR_self),
    MP_ROM_QSTR(MP_QSTR_buf),
    MP_ROM_QSTR(MP_QSTR_x),
    MP_ROM_QSTR(MP_QSTR_y),
    MP_ROM_QSTR(MP_QSTR_w),
    MP_ROM_QSTR(MP_QSTR_h),
};
STATIC const mp_raw_code_t raw_code_lcd160cr__lt_module_gt__LCD160CR_screen_dump = {
    .kind = MP_CODE_BYTECODE,
    .scope_flags = 0x00,
    .n_pos_args = 6,
    .fun_data = fun_data_lcd160cr__lt_module_gt__LCD160CR_screen_dump,
    .const_table = (mp_uint_t*)const_table_data_lcd160cr__lt_module_gt__LCD160CR_screen_dump,
    #if MICROPY_PERSISTENT_CODE_SAVE
    .fun_data_len = 259,
    .n_obj = 0,
    .n_raw_code = 0,
    #if MICROPY_PY_SYS_SETTRACE
    .prelude = {
        .n_state = 19,
        .n_exc_stack = 0,
        .scope_flags = 0,
        .n_pos_args = 6,
        .n_kwonly_args = 0,
        .n_def_pos_args = 4,
        .qstr_block_name = MP_QSTR_screen_dump,
        .qstr_source_file = MP_QSTR_lcd160cr_dot_py,
        .line_info = fun_data_lcd160cr__lt_module_gt__LCD160CR_screen_dump + 0,
        .opcodes = fun_data_lcd160cr__lt_module_gt__LCD160CR_screen_dump + 30,
    },
    .line_of_definition = 0,
    #endif
    #if MICROPY_EMIT_MACHINE_CODE
    .prelude_offset = 0,
    .n_qstr = 0,
    .qstr_link = NULL,
    #endif
    #endif
    #if MICROPY_EMIT_MACHINE_CODE
    .type_sig = 0,
    #endif
};

// frozen bytecode for file lcd160cr.py, scope lcd160cr__lt_module_gt__LCD160CR_screen_load
STATIC const byte fun_data_lcd160cr__lt_module_gt__LCD160CR_screen_load[168] = {
    0x62, 0x24,
    MP_QSTR_screen_load & 0xff, MP_QSTR_screen_load >> 8,
    MP_QSTR_lcd160cr_dot_py & 0xff, MP_QSTR_lcd160cr_dot_py >> 8,
    0x90, 0x26, 0x2e, 0x37, 0x22, 0x27, 0x23, 0x2f, 0x31, 0x49, 0x2d, 0x23, 0x29, 0x00,
    0xb0, 
    0x13, MP_QSTR_w & 0xff, MP_QSTR_w >> 8, 
    0xb0, 
    0x13, MP_QSTR_h & 0xff, MP_QSTR_h >> 8, 
    0xf4, 
    0x82, 
    0xf4, 
    0x82, 
    0xf2, 
    0xc2, 
    0xb0, 
    0x14, MP_QSTR__fcmd2b & 0xff, MP_QSTR__fcmd2b >> 8, 
    0x10, MP_QSTR__lt_BBHBBB & 0xff, MP_QSTR__lt_BBHBBB >> 8, 
    0x22, 0x80, 0x70, 
    0xb2, 
    0x90, 
    0xb0, 
    0x13, MP_QSTR_w & 0xff, MP_QSTR_w >> 8, 
    0xb0, 
    0x13, MP_QSTR_h & 0xff, MP_QSTR_h >> 8, 
    0x36, 0x06, 
    0x59, 
    0x80, 
    0xc3, 
    0x12, MP_QSTR_memoryview & 0xff, MP_QSTR_memoryview >> 8, 
    0xb1, 
    0x34, 0x01, 
    0xc4, 
    0x42, 0x56, 0x80, 
    0x12, MP_QSTR_len & 0xff, MP_QSTR_len >> 8, 
    0xb1, 
    0x34, 0x01, 
    0xb3, 
    0xf3, 
    0x22, 0x84, 0x00, 
    0xdb, 
    0x44, 0x1a, 0x80, 
    0xb0, 
    0x14, MP_QSTR__send & 0xff, MP_QSTR__send >> 8, 
    0xb4, 
    0xb3, 
    0xb3, 
    0x22, 0x84, 0x00, 
    0xf2, 
    0x2e, 0x02, 
    0x55, 
    0x36, 0x01, 
    0x59, 
    0xb3, 
    0x22, 0x84, 0x00, 
    0xe5, 
    0xc3, 
    0x42, 0x2d, 0x80, 
    0xb0, 
    0x14, MP_QSTR__send & 0xff, MP_QSTR__send >> 8, 
    0xb4, 
    0xb3, 
    0x51, 
    0x2e, 0x02, 
    0x55, 
    0x36, 0x01, 
    0x59, 
    0x42, 0x0d, 0x80, 
    0xb0, 
    0x14, MP_QSTR__send & 0xff, MP_QSTR__send >> 8, 
    0x23, 0x02, 
    0x36, 0x01, 
    0x59, 
    0xb3, 
    0x81, 
    0xe5, 
    0xc3, 
    0xb3, 
    0xb0, 
    0x13, MP_QSTR_w & 0xff, MP_QSTR_w >> 8, 
    0xb0, 
    0x13, MP_QSTR_h & 0xff, MP_QSTR_h >> 8, 
    0xf4, 
    0x82, 
    0xf4, 
    0xd7, 
    0x43, 0xe3, 0x7f, 
    0xb3, 
    0x12, MP_QSTR_len & 0xff, MP_QSTR_len >> 8, 
    0xb1, 
    0x34, 0x01, 
    0xd7, 
    0x43, 0x9f, 0x7f, 
    0x51, 
    0x63, 
};
STATIC const mp_obj_str_t const_obj_lcd160cr__lt_module_gt__LCD160CR_screen_load_0 = {{&mp_type_bytes}, 46501, 1, (const byte*)"\x00"};
STATIC const mp_rom_obj_t const_table_data_lcd160cr__lt_module_gt__LCD160CR_screen_load[3] = {
    MP_ROM_QSTR(MP_QSTR_self),
    MP_ROM_QSTR(MP_QSTR_buf),
    MP_ROM_PTR(&const_obj_lcd160cr__lt_module_gt__LCD160CR_screen_load_0),
};
STATIC const mp_raw_code_t raw_code_lcd160cr__lt_module_gt__LCD160CR_screen_load = {
    .kind = MP_CODE_BYTECODE,
    .scope_flags = 0x00,
    .n_pos_args = 2,
    .fun_data = fun_data_lcd160cr__lt_module_gt__LCD160CR_screen_load,
    .const_table = (mp_uint_t*)const_table_data_lcd160cr__lt_module_gt__LCD160CR_screen_load,
    #if MICROPY_PERSISTENT_CODE_SAVE
    .fun_data_len = 168,
    .n_obj = 1,
    .n_raw_code = 0,
    #if MICROPY_PY_SYS_SETTRACE
    .prelude = {
        .n_state = 13,
        .n_exc_stack = 0,
        .scope_flags = 0,
        .n_pos_args = 2,
        .n_kwonly_args = 0,
        .n_def_pos_args = 0,
        .qstr_block_name = MP_QSTR_screen_load,
        .qstr_source_file = MP_QSTR_lcd160cr_dot_py,
        .line_info = fun_data_lcd160cr__lt_module_gt__LCD160CR_screen_load + 0,
        .opcodes = fun_data_lcd160cr__lt_module_gt__LCD160CR_screen_load + 20,
    },
    .line_of_definition = 0,
    #endif
    #if MICROPY_EMIT_MACHINE_CODE
    .prelude_offset = 0,
    .n_qstr = 0,
    .qstr_link = NULL,
    #endif
    #endif
    #if MICROPY_EMIT_MACHINE_CODE
    .type_sig = 0,
    #endif
};

// frozen bytecode for file lcd160cr.py, scope lcd160cr__lt_module_gt__LCD160CR_set_pos
STATIC const byte fun_data_lcd160cr__lt_module_gt__LCD160CR_set_pos[26] = {
    0x43, 0x0e,
    MP_QSTR_set_pos & 0xff, MP_QSTR_set_pos >> 8,
    MP_QSTR_lcd160cr_dot_py & 0xff, MP_QSTR_lcd160cr_dot_py >> 8,
    0x90, 0x37, 0x00,
    0xb0, 
    0x14, MP_QSTR__fcmd2 & 0xff, MP_QSTR__fcmd2 >> 8, 
    0x10, MP_QSTR__lt_BBBB & 0xff, MP_QSTR__lt_BBBB >> 8, 
    0x22, 0x80, 0x58, 
    0xb1, 
    0xb2, 
    0x36, 0x04, 
    0x59, 
    0x51, 
    0x63, 
};
STATIC const mp_rom_obj_t const_table_data_lcd160cr__lt_module_gt__LCD160CR_set_pos[3] = {
    MP_ROM_QSTR(MP_QSTR_self),
    MP_ROM_QSTR(MP_QSTR_x),
    MP_ROM_QSTR(MP_QSTR_y),
};
STATIC const mp_raw_code_t raw_code_lcd160cr__lt_module_gt__LCD160CR_set_pos = {
    .kind = MP_CODE_BYTECODE,
    .scope_flags = 0x00,
    .n_pos_args = 3,
    .fun_data = fun_data_lcd160cr__lt_module_gt__LCD160CR_set_pos,
    .const_table = (mp_uint_t*)const_table_data_lcd160cr__lt_module_gt__LCD160CR_set_pos,
    #if MICROPY_PERSISTENT_CODE_SAVE
    .fun_data_len = 26,
    .n_obj = 0,
    .n_raw_code = 0,
    #if MICROPY_PY_SYS_SETTRACE
    .prelude = {
        .n_state = 9,
        .n_exc_stack = 0,
        .scope_flags = 0,
        .n_pos_args = 3,
        .n_kwonly_args = 0,
        .n_def_pos_args = 0,
        .qstr_block_name = MP_QSTR_set_pos,
        .qstr_source_file = MP_QSTR_lcd160cr_dot_py,
        .line_info = fun_data_lcd160cr__lt_module_gt__LCD160CR_set_pos + 0,
        .opcodes = fun_data_lcd160cr__lt_module_gt__LCD160CR_set_pos + 9,
    },
    .line_of_definition = 0,
    #endif
    #if MICROPY_EMIT_MACHINE_CODE
    .prelude_offset = 0,
    .n_qstr = 0,
    .qstr_link = NULL,
    #endif
    #endif
    #if MICROPY_EMIT_MACHINE_CODE
    .type_sig = 0,
    #endif
};

// frozen bytecode for file lcd160cr.py, scope lcd160cr__lt_module_gt__LCD160CR_set_text_color
STATIC const byte fun_data_lcd160cr__lt_module_gt__LCD160CR_set_text_color[26] = {
    0x43, 0x0e,
    MP_QSTR_set_text_color & 0xff, MP_QSTR_set_text_color >> 8,
    MP_QSTR_lcd160cr_dot_py & 0xff, MP_QSTR_lcd160cr_dot_py >> 8,
    0x90, 0x3a, 0x00,
    0xb0, 
    0x14, MP_QSTR__fcmd2 & 0xff, MP_QSTR__fcmd2 >> 8, 
    0x10, MP_QSTR__lt_BBHH & 0xff, MP_QSTR__lt_BBHH >> 8, 
    0x22, 0x80, 0x63, 
    0xb1, 
    0xb2, 
    0x36, 0x04, 
    0x59, 
    0x51, 
    0x63, 
};
STATIC const mp_rom_obj_t const_table_data_lcd160cr__lt_module_gt__LCD160CR_set_text_color[3] = {
    MP_ROM_QSTR(MP_QSTR_self),
    MP_ROM_QSTR(MP_QSTR_fg),
    MP_ROM_QSTR(MP_QSTR_bg),
};
STATIC const mp_raw_code_t raw_code_lcd160cr__lt_module_gt__LCD160CR_set_text_color = {
    .kind = MP_CODE_BYTECODE,
    .scope_flags = 0x00,
    .n_pos_args = 3,
    .fun_data = fun_data_lcd160cr__lt_module_gt__LCD160CR_set_text_color,
    .const_table = (mp_uint_t*)const_table_data_lcd160cr__lt_module_gt__LCD160CR_set_text_color,
    #if MICROPY_PERSISTENT_CODE_SAVE
    .fun_data_len = 26,
    .n_obj = 0,
    .n_raw_code = 0,
    #if MICROPY_PY_SYS_SETTRACE
    .prelude = {
        .n_state = 9,
        .n_exc_stack = 0,
        .scope_flags = 0,
        .n_pos_args = 3,
        .n_kwonly_args = 0,
        .n_def_pos_args = 0,
        .qstr_block_name = MP_QSTR_set_text_color,
        .qstr_source_file = MP_QSTR_lcd160cr_dot_py,
        .line_info = fun_data_lcd160cr__lt_module_gt__LCD160CR_set_text_color + 0,
        .opcodes = fun_data_lcd160cr__lt_module_gt__LCD160CR_set_text_color + 9,
    },
    .line_of_definition = 0,
    #endif
    #if MICROPY_EMIT_MACHINE_CODE
    .prelude_offset = 0,
    .n_qstr = 0,
    .qstr_link = NULL,
    #endif
    #endif
    #if MICROPY_EMIT_MACHINE_CODE
    .type_sig = 0,
    #endif
};

// frozen bytecode for file lcd160cr.py, scope lcd160cr__lt_module_gt__LCD160CR_set_font
STATIC const byte fun_data_lcd160cr__lt_module_gt__LCD160CR_set_font[49] = {
    0xe2, 0x84, 0x80, 0x01, 0x0e,
    MP_QSTR_set_font & 0xff, MP_QSTR_set_font >> 8,
    MP_QSTR_lcd160cr_dot_py & 0xff, MP_QSTR_lcd160cr_dot_py >> 8,
    0x90, 0x3d, 0x00,
    0xb0, 
    0x14, MP_QSTR__fcmd2 & 0xff, MP_QSTR__fcmd2 >> 8, 
    0x10, MP_QSTR__lt_BBBB & 0xff, MP_QSTR__lt_BBBB >> 8, 
    0x22, 0x80, 0x46, 
    0xb5, 
    0x87, 
    0xf0, 
    0xb4, 
    0x86, 
    0xf0, 
    0xed, 
    0xb1, 
    0x83, 
    0xef, 
    0x84, 
    0xf0, 
    0xed, 
    0xb3, 
    0x8f, 
    0xef, 
    0xed, 
    0xb2, 
    0x22, 0x81, 0x7f, 
    0xef, 
    0x36, 0x04, 
    0x59, 
    0x51, 
    0x63, 
};
STATIC const mp_rom_obj_t const_table_data_lcd160cr__lt_module_gt__LCD160CR_set_font[6] = {
    MP_ROM_QSTR(MP_QSTR_self),
    MP_ROM_QSTR(MP_QSTR_font),
    MP_ROM_QSTR(MP_QSTR_scale),
    MP_ROM_QSTR(MP_QSTR_bold),
    MP_ROM_QSTR(MP_QSTR_trans),
    MP_ROM_QSTR(MP_QSTR_scroll),
};
STATIC const mp_raw_code_t raw_code_lcd160cr__lt_module_gt__LCD160CR_set_font = {
    .kind = MP_CODE_BYTECODE,
    .scope_flags = 0x00,
    .n_pos_args = 6,
    .fun_data = fun_data_lcd160cr__lt_module_gt__LCD160CR_set_font,
    .const_table = (mp_uint_t*)const_table_data_lcd160cr__lt_module_gt__LCD160CR_set_font,
    #if MICROPY_PERSISTENT_CODE_SAVE
    .fun_data_len = 49,
    .n_obj = 0,
    .n_raw_code = 0,
    #if MICROPY_PY_SYS_SETTRACE
    .prelude = {
        .n_state = 13,
        .n_exc_stack = 0,
        .scope_flags = 0,
        .n_pos_args = 6,
        .n_kwonly_args = 0,
        .n_def_pos_args = 4,
        .qstr_block_name = MP_QSTR_set_font,
        .qstr_source_file = MP_QSTR_lcd160cr_dot_py,
        .line_info = fun_data_lcd160cr__lt_module_gt__LCD160CR_set_font + 0,
        .opcodes = fun_data_lcd160cr__lt_module_gt__LCD160CR_set_font + 12,
    },
    .line_of_definition = 0,
    #endif
    #if MICROPY_EMIT_MACHINE_CODE
    .prelude_offset = 0,
    .n_qstr = 0,
    .qstr_link = NULL,
    #endif
    #endif
    #if MICROPY_EMIT_MACHINE_CODE
    .type_sig = 0,
    #endif
};

// frozen bytecode for file lcd160cr.py, scope lcd160cr__lt_module_gt__LCD160CR_write
STATIC const byte fun_data_lcd160cr__lt_module_gt__LCD160CR_write[19] = {
    0x22, 0x0e,
    MP_QSTR_write & 0xff, MP_QSTR_write >> 8,
    MP_QSTR_lcd160cr_dot_py & 0xff, MP_QSTR_lcd160cr_dot_py >> 8,
    0x90, 0x41, 0x00,
    0xb0, 
    0x14, MP_QSTR__send & 0xff, MP_QSTR__send >> 8, 
    0xb1, 
    0x36, 0x01, 
    0x59, 
    0x51, 
    0x63, 
};
STATIC const mp_rom_obj_t const_table_data_lcd160cr__lt_module_gt__LCD160CR_write[2] = {
    MP_ROM_QSTR(MP_QSTR_self),
    MP_ROM_QSTR(MP_QSTR_s),
};
STATIC const mp_raw_code_t raw_code_lcd160cr__lt_module_gt__LCD160CR_write = {
    .kind = MP_CODE_BYTECODE,
    .scope_flags = 0x00,
    .n_pos_args = 2,
    .fun_data = fun_data_lcd160cr__lt_module_gt__LCD160CR_write,
    .const_table = (mp_uint_t*)const_table_data_lcd160cr__lt_module_gt__LCD160CR_write,
    #if MICROPY_PERSISTENT_CODE_SAVE
    .fun_data_len = 19,
    .n_obj = 0,
    .n_raw_code = 0,
    #if MICROPY_PY_SYS_SETTRACE
    .prelude = {
        .n_state = 5,
        .n_exc_stack = 0,
        .scope_flags = 0,
        .n_pos_args = 2,
        .n_kwonly_args = 0,
        .n_def_pos_args = 0,
        .qstr_block_name = MP_QSTR_write,
        .qstr_source_file = MP_QSTR_lcd160cr_dot_py,
        .line_info = fun_data_lcd160cr__lt_module_gt__LCD160CR_write + 0,
        .opcodes = fun_data_lcd160cr__lt_module_gt__LCD160CR_write + 9,
    },
    .line_of_definition = 0,
    #endif
    #if MICROPY_EMIT_MACHINE_CODE
    .prelude_offset = 0,
    .n_qstr = 0,
    .qstr_link = NULL,
    #endif
    #endif
    #if MICROPY_EMIT_MACHINE_CODE
    .type_sig = 0,
    #endif
};

// frozen bytecode for file lcd160cr.py, scope lcd160cr__lt_module_gt__LCD160CR_set_pen
STATIC const byte fun_data_lcd160cr__lt_module_gt__LCD160CR_set_pen[26] = {
    0x43, 0x0e,
    MP_QSTR_set_pen & 0xff, MP_QSTR_set_pen >> 8,
    MP_QSTR_lcd160cr_dot_py & 0xff, MP_QSTR_lcd160cr_dot_py >> 8,
    0x90, 0x46, 0x00,
    0xb0, 
    0x14, MP_QSTR__fcmd2 & 0xff, MP_QSTR__fcmd2 >> 8, 
    0x10, MP_QSTR__lt_BBHH & 0xff, MP_QSTR__lt_BBHH >> 8, 
    0x22, 0x80, 0x50, 
    0xb1, 
    0xb2, 
    0x36, 0x04, 
    0x59, 
    0x51, 
    0x63, 
};
STATIC const mp_rom_obj_t const_table_data_lcd160cr__lt_module_gt__LCD160CR_set_pen[3] = {
    MP_ROM_QSTR(MP_QSTR_self),
    MP_ROM_QSTR(MP_QSTR_line),
    MP_ROM_QSTR(MP_QSTR_fill),
};
STATIC const mp_raw_code_t raw_code_lcd160cr__lt_module_gt__LCD160CR_set_pen = {
    .kind = MP_CODE_BYTECODE,
    .scope_flags = 0x00,
    .n_pos_args = 3,
    .fun_data = fun_data_lcd160cr__lt_module_gt__LCD160CR_set_pen,
    .const_table = (mp_uint_t*)const_table_data_lcd160cr__lt_module_gt__LCD160CR_set_pen,
    #if MICROPY_PERSISTENT_CODE_SAVE
    .fun_data_len = 26,
    .n_obj = 0,
    .n_raw_code = 0,
    #if MICROPY_PY_SYS_SETTRACE
    .prelude = {
        .n_state = 9,
        .n_exc_stack = 0,
        .scope_flags = 0,
        .n_pos_args = 3,
        .n_kwonly_args = 0,
        .n_def_pos_args = 0,
        .qstr_block_name = MP_QSTR_set_pen,
        .qstr_source_file = MP_QSTR_lcd160cr_dot_py,
        .line_info = fun_data_lcd160cr__lt_module_gt__LCD160CR_set_pen + 0,
        .opcodes = fun_data_lcd160cr__lt_module_gt__LCD160CR_set_pen + 9,
    },
    .line_of_definition = 0,
    #endif
    #if MICROPY_EMIT_MACHINE_CODE
    .prelude_offset = 0,
    .n_qstr = 0,
    .qstr_link = NULL,
    #endif
    #endif
    #if MICROPY_EMIT_MACHINE_CODE
    .type_sig = 0,
    #endif
};

// frozen bytecode for file lcd160cr.py, scope lcd160cr__lt_module_gt__LCD160CR_erase
STATIC const byte fun_data_lcd160cr__lt_module_gt__LCD160CR_erase[20] = {
    0x19, 0x0e,
    MP_QSTR_erase & 0xff, MP_QSTR_erase >> 8,
    MP_QSTR_lcd160cr_dot_py & 0xff, MP_QSTR_lcd160cr_dot_py >> 8,
    0x90, 0x49, 0x00,
    0xb0, 
    0x14, MP_QSTR__send & 0xff, MP_QSTR__send >> 8, 
    0x23, 0x01, 
    0x36, 0x01, 
    0x59, 
    0x51, 
    0x63, 
};
STATIC const mp_obj_str_t const_obj_lcd160cr__lt_module_gt__LCD160CR_erase_0 = {{&mp_type_bytes}, 27330, 2, (const byte*)"\x02\x45"};
STATIC const mp_rom_obj_t const_table_data_lcd160cr__lt_module_gt__LCD160CR_erase[2] = {
    MP_ROM_QSTR(MP_QSTR_self),
    MP_ROM_PTR(&const_obj_lcd160cr__lt_module_gt__LCD160CR_erase_0),
};
STATIC const mp_raw_code_t raw_code_lcd160cr__lt_module_gt__LCD160CR_erase = {
    .kind = MP_CODE_BYTECODE,
    .scope_flags = 0x00,
    .n_pos_args = 1,
    .fun_data = fun_data_lcd160cr__lt_module_gt__LCD160CR_erase,
    .const_table = (mp_uint_t*)const_table_data_lcd160cr__lt_module_gt__LCD160CR_erase,
    #if MICROPY_PERSISTENT_CODE_SAVE
    .fun_data_len = 20,
    .n_obj = 1,
    .n_raw_code = 0,
    #if MICROPY_PY_SYS_SETTRACE
    .prelude = {
        .n_state = 4,
        .n_exc_stack = 0,
        .scope_flags = 0,
        .n_pos_args = 1,
        .n_kwonly_args = 0,
        .n_def_pos_args = 0,
        .qstr_block_name = MP_QSTR_erase,
        .qstr_source_file = MP_QSTR_lcd160cr_dot_py,
        .line_info = fun_data_lcd160cr__lt_module_gt__LCD160CR_erase + 0,
        .opcodes = fun_data_lcd160cr__lt_module_gt__LCD160CR_erase + 9,
    },
    .line_of_definition = 0,
    #endif
    #if MICROPY_EMIT_MACHINE_CODE
    .prelude_offset = 0,
    .n_qstr = 0,
    .qstr_link = NULL,
    #endif
    #endif
    #if MICROPY_EMIT_MACHINE_CODE
    .type_sig = 0,
    #endif
};

// frozen bytecode for file lcd160cr.py, scope lcd160cr__lt_module_gt__LCD160CR_dot
STATIC const byte fun_data_lcd160cr__lt_module_gt__LCD160CR_dot[70] = {
    0x43, 0x12,
    MP_QSTR_dot & 0xff, MP_QSTR_dot >> 8,
    MP_QSTR_lcd160cr_dot_py & 0xff, MP_QSTR_lcd160cr_dot_py >> 8,
    0x90, 0x4c, 0x1f, 0x2b, 0x00,
    0x80, 
    0xb1, 
    0x57, 
    0x5b, 
    0xda, 
    0x46, 0x08, 0x80, 
    0xb0, 
    0x13, MP_QSTR_w & 0xff, MP_QSTR_w >> 8, 
    0xd7, 
    0x42, 0x02, 0x80, 
    0x5a, 
    0x59, 
    0x44, 0x24, 0x80, 
    0x80, 
    0xb2, 
    0x57, 
    0x5b, 
    0xda, 
    0x46, 0x08, 0x80, 
    0xb0, 
    0x13, MP_QSTR_h & 0xff, MP_QSTR_h >> 8, 
    0xd7, 
    0x42, 0x02, 0x80, 
    0x5a, 
    0x59, 
    0x44, 0x0f, 0x80, 
    0xb0, 
    0x14, MP_QSTR__fcmd2 & 0xff, MP_QSTR__fcmd2 >> 8, 
    0x10, MP_QSTR__lt_BBBB & 0xff, MP_QSTR__lt_BBBB >> 8, 
    0x22, 0x80, 0x4b, 
    0xb1, 
    0xb2, 
    0x36, 0x04, 
    0x59, 
    0x51, 
    0x63, 
};
STATIC const mp_rom_obj_t const_table_data_lcd160cr__lt_module_gt__LCD160CR_dot[3] = {
    MP_ROM_QSTR(MP_QSTR_self),
    MP_ROM_QSTR(MP_QSTR_x),
    MP_ROM_QSTR(MP_QSTR_y),
};
STATIC const mp_raw_code_t raw_code_lcd160cr__lt_module_gt__LCD160CR_dot = {
    .kind = MP_CODE_BYTECODE,
    .scope_flags = 0x00,
    .n_pos_args = 3,
    .fun_data = fun_data_lcd160cr__lt_module_gt__LCD160CR_dot,
    .const_table = (mp_uint_t*)const_table_data_lcd160cr__lt_module_gt__LCD160CR_dot,
    #if MICROPY_PERSISTENT_CODE_SAVE
    .fun_data_len = 70,
    .n_obj = 0,
    .n_raw_code = 0,
    #if MICROPY_PY_SYS_SETTRACE
    .prelude = {
        .n_state = 9,
        .n_exc_stack = 0,
        .scope_flags = 0,
        .n_pos_args = 3,
        .n_kwonly_args = 0,
        .n_def_pos_args = 0,
        .qstr_block_name = MP_QSTR_dot,
        .qstr_source_file = MP_QSTR_lcd160cr_dot_py,
        .line_info = fun_data_lcd160cr__lt_module_gt__LCD160CR_dot + 0,
        .opcodes = fun_data_lcd160cr__lt_module_gt__LCD160CR_dot + 11,
    },
    .line_of_definition = 0,
    #endif
    #if MICROPY_EMIT_MACHINE_CODE
    .prelude_offset = 0,
    .n_qstr = 0,
    .qstr_link = NULL,
    #endif
    #endif
    #if MICROPY_EMIT_MACHINE_CODE
    .type_sig = 0,
    #endif
};

// frozen bytecode for file lcd160cr.py, scope lcd160cr__lt_module_gt__LCD160CR_rect
STATIC const byte fun_data_lcd160cr__lt_module_gt__LCD160CR_rect[350] = {
    0x8a, 0x15, 0x40,
    MP_QSTR_rect & 0xff, MP_QSTR_rect >> 8,
    MP_QSTR_lcd160cr_dot_py & 0xff, MP_QSTR_lcd160cr_dot_py >> 8,
    0x90, 0x50, 0x1f, 0x23, 0x22, 0x2c, 0x24, 0x26, 0x22, 0x24, 0x22, 0x26, 0x22, 0x24, 0x22, 0x50, 0x1f, 0x22, 0x50, 0x24, 0x39, 0x24, 0x39, 0x2b, 0x3b, 0x2b, 0x5e, 0x00,
    0xb1, 
    0xb3, 
    0xf2, 
    0x80, 
    0xda, 
    0x43, 0x1a, 0x80, 
    0xb2, 
    0xb4, 
    0xf2, 
    0x80, 
    0xda, 
    0x43, 0x12, 0x80, 
    0xb1, 
    0xb0, 
    0x13, MP_QSTR_w & 0xff, MP_QSTR_w >> 8, 
    0xdb, 
    0x43, 0x09, 0x80, 
    0xb2, 
    0xb0, 
    0x13, MP_QSTR_h & 0xff, MP_QSTR_h >> 8, 
    0xdb, 
    0x44, 0x02, 0x80, 
    0x51, 
    0x63, 
    0xb1, 
    0x80, 
    0xd7, 
    0x43, 0x06, 0x80, 
    0xb2, 
    0x80, 
    0xd7, 
    0x44, 0xea, 0x80, 
    0x52, 
    0x57, 
    0xc6, 
    0xc7, 
    0xb1, 
    0x80, 
    0xd7, 
    0x44, 0x08, 0x80, 
    0x50, 
    0xc6, 
    0xb3, 
    0xb1, 
    0xe5, 
    0xc3, 
    0x80, 
    0xc1, 
    0xb2, 
    0x80, 
    0xd7, 
    0x44, 0x08, 0x80, 
    0x50, 
    0xc7, 
    0xb4, 
    0xb2, 
    0xe5, 
    0xc4, 
    0x80, 
    0xc2, 
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
    0x14, MP_QSTR__fcmd2b & 0xff, MP_QSTR__fcmd2b >> 8, 
    0x10, MP_QSTR__lt_BBBBBB & 0xff, MP_QSTR__lt_BBBBBB >> 8, 
    0x22, 0x80, 0x51, 
    0xb1, 
    0xb2, 
    0x12, MP_QSTR_min & 0xff, MP_QSTR_min >> 8, 
    0xb3, 
    0x22, 0x81, 0x7f, 
    0x34, 0x02, 
    0x12, MP_QSTR_min & 0xff, MP_QSTR_min >> 8, 
    0xb4, 
    0x22, 0x81, 0x7f, 
    0x34, 0x02, 
    0x36, 0x06, 
    0x59, 
    0xb5, 
    0x22, 0x80, 0x57, 
    0xd9, 
    0x43, 0x08, 0x80, 
    0xb5, 
    0x22, 0x80, 0x72, 
    0xd9, 
    0x44, 0x86, 0x80, 
    0xb6, 
    0x44, 0x19, 0x80, 
    0xb0, 
    0x14, MP_QSTR__fcmd2b & 0xff, MP_QSTR__fcmd2b >> 8, 
    0x10, MP_QSTR__lt_BBBBBB & 0xff, MP_QSTR__lt_BBBBBB >> 8, 
    0x22, 0x80, 0x57, 
    0xb1, 
    0xb2, 
    0x81, 
    0x12, MP_QSTR_min & 0xff, MP_QSTR_min >> 8, 
    0xb4, 
    0x22, 0x81, 0x7f, 
    0x34, 0x02, 
    0x36, 0x06, 
    0x59, 
    0xb7, 
    0x44, 0x19, 0x80, 
    0xb0, 
    0x14, MP_QSTR__fcmd2b & 0xff, MP_QSTR__fcmd2b >> 8, 
    0x10, MP_QSTR__lt_BBBBBB & 0xff, MP_QSTR__lt_BBBBBB >> 8, 
    0x22, 0x80, 0x57, 
    0xb1, 
    0xb2, 
    0x12, MP_QSTR_min & 0xff, MP_QSTR_min >> 8, 
    0xb3, 
    0x22, 0x81, 0x7f, 
    0x34, 0x02, 
    0x81, 
    0x36, 0x06, 
    0x59, 
    0xb1, 
    0xb3, 
    0xf2, 
    0xb0, 
    0x13, MP_QSTR_w & 0xff, MP_QSTR_w >> 8, 
    0xd7, 
    0x44, 0x1b, 0x80, 
    0xb0, 
    0x14, MP_QSTR__fcmd2b & 0xff, MP_QSTR__fcmd2b >> 8, 
    0x10, MP_QSTR__lt_BBBBBB & 0xff, MP_QSTR__lt_BBBBBB >> 8, 
    0x22, 0x80, 0x57, 
    0xb1, 
    0xb3, 
    0xf2, 
    0xb2, 
    0x81, 
    0x12, MP_QSTR_min & 0xff, MP_QSTR_min >> 8, 
    0xb4, 
    0x22, 0x81, 0x7f, 
    0x34, 0x02, 
    0x36, 0x06, 
    0x59, 
    0xb2, 
    0xb4, 
    0xf2, 
    0xb0, 
    0x13, MP_QSTR_h & 0xff, MP_QSTR_h >> 8, 
    0xd7, 
    0x44, 0x1b, 0x80, 
    0xb0, 
    0x14, MP_QSTR__fcmd2b & 0xff, MP_QSTR__fcmd2b >> 8, 
    0x10, MP_QSTR__lt_BBBBBB & 0xff, MP_QSTR__lt_BBBBBB >> 8, 
    0x22, 0x80, 0x57, 
    0xb1, 
    0xb2, 
    0xb4, 
    0xf2, 
    0x12, MP_QSTR_min & 0xff, MP_QSTR_min >> 8, 
    0xb3, 
    0x22, 0x81, 0x7f, 
    0x34, 0x02, 
    0x81, 
    0x36, 0x06, 
    0x59, 
    0x42, 0x1f, 0x80, 
    0xb0, 
    0x14, MP_QSTR__fcmd2b & 0xff, MP_QSTR__fcmd2b >> 8, 
    0x10, MP_QSTR__lt_BBBBBB & 0xff, MP_QSTR__lt_BBBBBB >> 8, 
    0xb5, 
    0xb1, 
    0xb2, 
    0x12, MP_QSTR_min & 0xff, MP_QSTR_min >> 8, 
    0xb3, 
    0x22, 0x81, 0x7f, 
    0x34, 0x02, 
    0x12, MP_QSTR_min & 0xff, MP_QSTR_min >> 8, 
    0xb4, 
    0x22, 0x81, 0x7f, 
    0x34, 0x02, 
    0x36, 0x06, 
    0x59, 
    0x51, 
    0x63, 
};
STATIC const mp_rom_obj_t const_table_data_lcd160cr__lt_module_gt__LCD160CR_rect[6] = {
    MP_ROM_QSTR(MP_QSTR_self),
    MP_ROM_QSTR(MP_QSTR_x),
    MP_ROM_QSTR(MP_QSTR_y),
    MP_ROM_QSTR(MP_QSTR_w),
    MP_ROM_QSTR(MP_QSTR_h),
    MP_ROM_QSTR(MP_QSTR_cmd),
};
STATIC const mp_raw_code_t raw_code_lcd160cr__lt_module_gt__LCD160CR_rect = {
    .kind = MP_CODE_BYTECODE,
    .scope_flags = 0x00,
    .n_pos_args = 6,
    .fun_data = fun_data_lcd160cr__lt_module_gt__LCD160CR_rect,
    .const_table = (mp_uint_t*)const_table_data_lcd160cr__lt_module_gt__LCD160CR_rect,
    #if MICROPY_PERSISTENT_CODE_SAVE
    .fun_data_len = 350,
    .n_obj = 0,
    .n_raw_code = 0,
    #if MICROPY_PY_SYS_SETTRACE
    .prelude = {
        .n_state = 18,
        .n_exc_stack = 0,
        .scope_flags = 0,
        .n_pos_args = 6,
        .n_kwonly_args = 0,
        .n_def_pos_args = 1,
        .qstr_block_name = MP_QSTR_rect,
        .qstr_source_file = MP_QSTR_lcd160cr_dot_py,
        .line_info = fun_data_lcd160cr__lt_module_gt__LCD160CR_rect + 0,
        .opcodes = fun_data_lcd160cr__lt_module_gt__LCD160CR_rect + 35,
    },
    .line_of_definition = 0,
    #endif
    #if MICROPY_EMIT_MACHINE_CODE
    .prelude_offset = 0,
    .n_qstr = 0,
    .qstr_link = NULL,
    #endif
    #endif
    #if MICROPY_EMIT_MACHINE_CODE
    .type_sig = 0,
    #endif
};

// frozen bytecode for file lcd160cr.py, scope lcd160cr__lt_module_gt__LCD160CR_rect_outline
STATIC const byte fun_data_lcd160cr__lt_module_gt__LCD160CR_rect_outline[26] = {
    0xd9, 0x04, 0x0e,
    MP_QSTR_rect_outline & 0xff, MP_QSTR_rect_outline >> 8,
    MP_QSTR_lcd160cr_dot_py & 0xff, MP_QSTR_lcd160cr_dot_py >> 8,
    0x90, 0x6d, 0x00,
    0xb0, 
    0x14, MP_QSTR_rect & 0xff, MP_QSTR_rect >> 8, 
    0xb1, 
    0xb2, 
    0xb3, 
    0xb4, 
    0x22, 0x80, 0x57, 
    0x36, 0x05, 
    0x59, 
    0x51, 
    0x63, 
};
STATIC const mp_rom_obj_t const_table_data_lcd160cr__lt_module_gt__LCD160CR_rect_outline[5] = {
    MP_ROM_QSTR(MP_QSTR_self),
    MP_ROM_QSTR(MP_QSTR_x),
    MP_ROM_QSTR(MP_QSTR_y),
    MP_ROM_QSTR(MP_QSTR_w),
    MP_ROM_QSTR(MP_QSTR_h),
};
STATIC const mp_raw_code_t raw_code_lcd160cr__lt_module_gt__LCD160CR_rect_outline = {
    .kind = MP_CODE_BYTECODE,
    .scope_flags = 0x00,
    .n_pos_args = 5,
    .fun_data = fun_data_lcd160cr__lt_module_gt__LCD160CR_rect_outline,
    .const_table = (mp_uint_t*)const_table_data_lcd160cr__lt_module_gt__LCD160CR_rect_outline,
    #if MICROPY_PERSISTENT_CODE_SAVE
    .fun_data_len = 26,
    .n_obj = 0,
    .n_raw_code = 0,
    #if MICROPY_PY_SYS_SETTRACE
    .prelude = {
        .n_state = 12,
        .n_exc_stack = 0,
        .scope_flags = 0,
        .n_pos_args = 5,
        .n_kwonly_args = 0,
        .n_def_pos_args = 0,
        .qstr_block_name = MP_QSTR_rect_outline,
        .qstr_source_file = MP_QSTR_lcd160cr_dot_py,
        .line_info = fun_data_lcd160cr__lt_module_gt__LCD160CR_rect_outline + 0,
        .opcodes = fun_data_lcd160cr__lt_module_gt__LCD160CR_rect_outline + 10,
    },
    .line_of_definition = 0,
    #endif
    #if MICROPY_EMIT_MACHINE_CODE
    .prelude_offset = 0,
    .n_qstr = 0,
    .qstr_link = NULL,
    #endif
    #endif
    #if MICROPY_EMIT_MACHINE_CODE
    .type_sig = 0,
    #endif
};

// frozen bytecode for file lcd160cr.py, scope lcd160cr__lt_module_gt__LCD160CR_rect_interior
STATIC const byte fun_data_lcd160cr__lt_module_gt__LCD160CR_rect_interior[26] = {
    0xd9, 0x04, 0x0e,
    MP_QSTR_rect_interior & 0xff, MP_QSTR_rect_interior >> 8,
    MP_QSTR_lcd160cr_dot_py & 0xff, MP_QSTR_lcd160cr_dot_py >> 8,
    0x90, 0x70, 0x00,
    0xb0, 
    0x14, MP_QSTR_rect & 0xff, MP_QSTR_rect >> 8, 
    0xb1, 
    0xb2, 
    0xb3, 
    0xb4, 
    0x22, 0x80, 0x51, 
    0x36, 0x05, 
    0x59, 
    0x51, 
    0x63, 
};
STATIC const mp_rom_obj_t const_table_data_lcd160cr__lt_module_gt__LCD160CR_rect_interior[5] = {
    MP_ROM_QSTR(MP_QSTR_self),
    MP_ROM_QSTR(MP_QSTR_x),
    MP_ROM_QSTR(MP_QSTR_y),
    MP_ROM_QSTR(MP_QSTR_w),
    MP_ROM_QSTR(MP_QSTR_h),
};
STATIC const mp_raw_code_t raw_code_lcd160cr__lt_module_gt__LCD160CR_rect_interior = {
    .kind = MP_CODE_BYTECODE,
    .scope_flags = 0x00,
    .n_pos_args = 5,
    .fun_data = fun_data_lcd160cr__lt_module_gt__LCD160CR_rect_interior,
    .const_table = (mp_uint_t*)const_table_data_lcd160cr__lt_module_gt__LCD160CR_rect_interior,
    #if MICROPY_PERSISTENT_CODE_SAVE
    .fun_data_len = 26,
    .n_obj = 0,
    .n_raw_code = 0,
    #if MICROPY_PY_SYS_SETTRACE
    .prelude = {
        .n_state = 12,
        .n_exc_stack = 0,
        .scope_flags = 0,
        .n_pos_args = 5,
        .n_kwonly_args = 0,
        .n_def_pos_args = 0,
        .qstr_block_name = MP_QSTR_rect_interior,
        .qstr_source_file = MP_QSTR_lcd160cr_dot_py,
        .line_info = fun_data_lcd160cr__lt_module_gt__LCD160CR_rect_interior + 0,
        .opcodes = fun_data_lcd160cr__lt_module_gt__LCD160CR_rect_interior + 10,
    },
    .line_of_definition = 0,
    #endif
    #if MICROPY_EMIT_MACHINE_CODE
    .prelude_offset = 0,
    .n_qstr = 0,
    .qstr_link = NULL,
    #endif
    #endif
    #if MICROPY_EMIT_MACHINE_CODE
    .type_sig = 0,
    #endif
};

// frozen bytecode for file lcd160cr.py, scope lcd160cr__lt_module_gt__LCD160CR_line
STATIC const byte fun_data_lcd160cr__lt_module_gt__LCD160CR_line[82] = {
    0xf1, 0x04, 0x1a,
    MP_QSTR_line & 0xff, MP_QSTR_line >> 8,
    MP_QSTR_lcd160cr_dot_py & 0xff, MP_QSTR_lcd160cr_dot_py >> 8,
    0x90, 0x73, 0x25, 0x24, 0x24, 0x24, 0x24, 0x32, 0x00,
    0xb0, 
    0x13, MP_QSTR_array4 & 0xff, MP_QSTR_array4 >> 8, 
    0xc5, 
    0xb1, 
    0xb5, 
    0x80, 
    0x56, 
    0xb2, 
    0xb5, 
    0x81, 
    0x56, 
    0xb3, 
    0xb5, 
    0x82, 
    0x56, 
    0xb4, 
    0xb5, 
    0x83, 
    0x56, 
    0xb0, 
    0x14, MP_QSTR_clip_line & 0xff, MP_QSTR_clip_line >> 8, 
    0xb5, 
    0xb0, 
    0x13, MP_QSTR_w & 0xff, MP_QSTR_w >> 8, 
    0xb0, 
    0x13, MP_QSTR_h & 0xff, MP_QSTR_h >> 8, 
    0x36, 0x03, 
    0x44, 0x19, 0x80, 
    0xb0, 
    0x14, MP_QSTR__fcmd2b & 0xff, MP_QSTR__fcmd2b >> 8, 
    0x10, MP_QSTR__lt_BBBBBB & 0xff, MP_QSTR__lt_BBBBBB >> 8, 
    0x22, 0x80, 0x4c, 
    0xb5, 
    0x80, 
    0x55, 
    0xb5, 
    0x81, 
    0x55, 
    0xb5, 
    0x82, 
    0x55, 
    0xb5, 
    0x83, 
    0x55, 
    0x36, 0x06, 
    0x59, 
    0x51, 
    0x63, 
};
STATIC const mp_rom_obj_t const_table_data_lcd160cr__lt_module_gt__LCD160CR_line[5] = {
    MP_ROM_QSTR(MP_QSTR_self),
    MP_ROM_QSTR(MP_QSTR_x1),
    MP_ROM_QSTR(MP_QSTR_y1),
    MP_ROM_QSTR(MP_QSTR_x2),
    MP_ROM_QSTR(MP_QSTR_y2),
};
STATIC const mp_raw_code_t raw_code_lcd160cr__lt_module_gt__LCD160CR_line = {
    .kind = MP_CODE_BYTECODE,
    .scope_flags = 0x00,
    .n_pos_args = 5,
    .fun_data = fun_data_lcd160cr__lt_module_gt__LCD160CR_line,
    .const_table = (mp_uint_t*)const_table_data_lcd160cr__lt_module_gt__LCD160CR_line,
    #if MICROPY_PERSISTENT_CODE_SAVE
    .fun_data_len = 82,
    .n_obj = 0,
    .n_raw_code = 0,
    #if MICROPY_PY_SYS_SETTRACE
    .prelude = {
        .n_state = 15,
        .n_exc_stack = 0,
        .scope_flags = 0,
        .n_pos_args = 5,
        .n_kwonly_args = 0,
        .n_def_pos_args = 0,
        .qstr_block_name = MP_QSTR_line,
        .qstr_source_file = MP_QSTR_lcd160cr_dot_py,
        .line_info = fun_data_lcd160cr__lt_module_gt__LCD160CR_line + 0,
        .opcodes = fun_data_lcd160cr__lt_module_gt__LCD160CR_line + 16,
    },
    .line_of_definition = 0,
    #endif
    #if MICROPY_EMIT_MACHINE_CODE
    .prelude_offset = 0,
    .n_qstr = 0,
    .qstr_link = NULL,
    #endif
    #endif
    #if MICROPY_EMIT_MACHINE_CODE
    .type_sig = 0,
    #endif
};

// frozen bytecode for file lcd160cr.py, scope lcd160cr__lt_module_gt__LCD160CR_dot_no_clip
STATIC const byte fun_data_lcd160cr__lt_module_gt__LCD160CR_dot_no_clip[26] = {
    0x43, 0x0e,
    MP_QSTR_dot_no_clip & 0xff, MP_QSTR_dot_no_clip >> 8,
    MP_QSTR_lcd160cr_dot_py & 0xff, MP_QSTR_lcd160cr_dot_py >> 8,
    0x90, 0x7c, 0x00,
    0xb0, 
    0x14, MP_QSTR__fcmd2 & 0xff, MP_QSTR__fcmd2 >> 8, 
    0x10, MP_QSTR__lt_BBBB & 0xff, MP_QSTR__lt_BBBB >> 8, 
    0x22, 0x80, 0x4b, 
    0xb1, 
    0xb2, 
    0x36, 0x04, 
    0x59, 
    0x51, 
    0x63, 
};
STATIC const mp_rom_obj_t const_table_data_lcd160cr__lt_module_gt__LCD160CR_dot_no_clip[3] = {
    MP_ROM_QSTR(MP_QSTR_self),
    MP_ROM_QSTR(MP_QSTR_x),
    MP_ROM_QSTR(MP_QSTR_y),
};
STATIC const mp_raw_code_t raw_code_lcd160cr__lt_module_gt__LCD160CR_dot_no_clip = {
    .kind = MP_CODE_BYTECODE,
    .scope_flags = 0x00,
    .n_pos_args = 3,
    .fun_data = fun_data_lcd160cr__lt_module_gt__LCD160CR_dot_no_clip,
    .const_table = (mp_uint_t*)const_table_data_lcd160cr__lt_module_gt__LCD160CR_dot_no_clip,
    #if MICROPY_PERSISTENT_CODE_SAVE
    .fun_data_len = 26,
    .n_obj = 0,
    .n_raw_code = 0,
    #if MICROPY_PY_SYS_SETTRACE
    .prelude = {
        .n_state = 9,
        .n_exc_stack = 0,
        .scope_flags = 0,
        .n_pos_args = 3,
        .n_kwonly_args = 0,
        .n_def_pos_args = 0,
        .qstr_block_name = MP_QSTR_dot_no_clip,
        .qstr_source_file = MP_QSTR_lcd160cr_dot_py,
        .line_info = fun_data_lcd160cr__lt_module_gt__LCD160CR_dot_no_clip + 0,
        .opcodes = fun_data_lcd160cr__lt_module_gt__LCD160CR_dot_no_clip + 9,
    },
    .line_of_definition = 0,
    #endif
    #if MICROPY_EMIT_MACHINE_CODE
    .prelude_offset = 0,
    .n_qstr = 0,
    .qstr_link = NULL,
    #endif
    #endif
    #if MICROPY_EMIT_MACHINE_CODE
    .type_sig = 0,
    #endif
};

// frozen bytecode for file lcd160cr.py, scope lcd160cr__lt_module_gt__LCD160CR_rect_no_clip
STATIC const byte fun_data_lcd160cr__lt_module_gt__LCD160CR_rect_no_clip[29] = {
    0xe1, 0x04, 0x0e,
    MP_QSTR_rect_no_clip & 0xff, MP_QSTR_rect_no_clip >> 8,
    MP_QSTR_lcd160cr_dot_py & 0xff, MP_QSTR_lcd160cr_dot_py >> 8,
    0x90, 0x7f, 0x00,
    0xb0, 
    0x14, MP_QSTR__fcmd2b & 0xff, MP_QSTR__fcmd2b >> 8, 
    0x10, MP_QSTR__lt_BBBBBB & 0xff, MP_QSTR__lt_BBBBBB >> 8, 
    0x22, 0x80, 0x72, 
    0xb1, 
    0xb2, 
    0xb3, 
    0xb4, 
    0x36, 0x06, 
    0x59, 
    0x51, 
    0x63, 
};
STATIC const mp_rom_obj_t const_table_data_lcd160cr__lt_module_gt__LCD160CR_rect_no_clip[5] = {
    MP_ROM_QSTR(MP_QSTR_self),
    MP_ROM_QSTR(MP_QSTR_x),
    MP_ROM_QSTR(MP_QSTR_y),
    MP_ROM_QSTR(MP_QSTR_w),
    MP_ROM_QSTR(MP_QSTR_h),
};
STATIC const mp_raw_code_t raw_code_lcd160cr__lt_module_gt__LCD160CR_rect_no_clip = {
    .kind = MP_CODE_BYTECODE,
    .scope_flags = 0x00,
    .n_pos_args = 5,
    .fun_data = fun_data_lcd160cr__lt_module_gt__LCD160CR_rect_no_clip,
    .const_table = (mp_uint_t*)const_table_data_lcd160cr__lt_module_gt__LCD160CR_rect_no_clip,
    #if MICROPY_PERSISTENT_CODE_SAVE
    .fun_data_len = 29,
    .n_obj = 0,
    .n_raw_code = 0,
    #if MICROPY_PY_SYS_SETTRACE
    .prelude = {
        .n_state = 13,
        .n_exc_stack = 0,
        .scope_flags = 0,
        .n_pos_args = 5,
        .n_kwonly_args = 0,
        .n_def_pos_args = 0,
        .qstr_block_name = MP_QSTR_rect_no_clip,
        .qstr_source_file = MP_QSTR_lcd160cr_dot_py,
        .line_info = fun_data_lcd160cr__lt_module_gt__LCD160CR_rect_no_clip + 0,
        .opcodes = fun_data_lcd160cr__lt_module_gt__LCD160CR_rect_no_clip + 10,
    },
    .line_of_definition = 0,
    #endif
    #if MICROPY_EMIT_MACHINE_CODE
    .prelude_offset = 0,
    .n_qstr = 0,
    .qstr_link = NULL,
    #endif
    #endif
    #if MICROPY_EMIT_MACHINE_CODE
    .type_sig = 0,
    #endif
};

// frozen bytecode for file lcd160cr.py, scope lcd160cr__lt_module_gt__LCD160CR_rect_outline_no_clip
STATIC const byte fun_data_lcd160cr__lt_module_gt__LCD160CR_rect_outline_no_clip[29] = {
    0xe1, 0x04, 0x0e,
    MP_QSTR_rect_outline_no_clip & 0xff, MP_QSTR_rect_outline_no_clip >> 8,
    MP_QSTR_lcd160cr_dot_py & 0xff, MP_QSTR_lcd160cr_dot_py >> 8,
    0x90, 0x82, 0x00,
    0xb0, 
    0x14, MP_QSTR__fcmd2b & 0xff, MP_QSTR__fcmd2b >> 8, 
    0x10, MP_QSTR__lt_BBBBBB & 0xff, MP_QSTR__lt_BBBBBB >> 8, 
    0x22, 0x80, 0x57, 
    0xb1, 
    0xb2, 
    0xb3, 
    0xb4, 
    0x36, 0x06, 
    0x59, 
    0x51, 
    0x63, 
};
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
