The-Ant-Lab/arcobaleno/firmware/build-ARCOBALENO_PLUS/pins_af.py

PINS_AF = (
  ('X1', (1, 'TIM2_CH3'), (2, 'TIM5_CH3'), (3, 'TIM9_CH1'), (7, 'USART2_TX'), ),
  ('X2', (1, 'TIM2_CH4'), (2, 'TIM5_CH4'), (3, 'TIM9_CH2'), (5, 'I2S2_MCK'), (7, 'USART2_RX'), ),
  ('X3', (1, 'TIM2_CH1'), (1, 'TIM2_ETR'), (2, 'TIM5_CH1'), (3, 'TIM8_ETR'), (7, 'USART2_CTS'), (8, 'UART4_TX'), ),
  ('X4', (1, 'TIM2_CH2'), (2, 'TIM5_CH2'), (5, 'SPI4_MOSI'), (5, 'I2S4_SD'), (7, 'USART2_RTS'), (8, 'UART4_RX'), ),
  ('X5', (5, 'SPI1_NSS'), (5, 'I2S1_WS'), (6, 'SPI3_NSS'), (6, 'I2S3_WS'), (7, 'USART2_CK'), ),
  ('X6', (1, 'TIM2_CH1'), (1, 'TIM2_ETR'), (3, 'TIM8_CH1N'), (5, 'SPI1_SCK'), (5, 'I2S1_CK'), ),
  ('X7', (1, 'TIM1_BKIN'), (2, 'TIM3_CH1'), (3, 'TIM8_BKIN'), (5, 'SPI1_MISO'), (6, 'I2S2_MCK'), (9, 'TIM13_CH1'), ),
  ('X8', (1, 'TIM1_CH1N'), (2, 'TIM3_CH2'), (3, 'TIM8_CH1N'), (5, 'SPI1_MOSI'), (5, 'I2S1_SD'), (9, 'TIM14_CH1'), ),
  ('X9', (2, 'TIM4_CH1'), (4, 'I2C1_SCL'), (7, 'USART1_TX'), (9, 'CAN2_TX'), (11, 'UART5_TX'), ),
  ('X10', (2, 'TIM4_CH2'), (4, 'I2C1_SDA'), (7, 'USART1_RX'), ),
  ('X11', (5, 'I2S1_MCK'), ),
  ('X12', (7, 'USART3_RX'), ),
  ('X17', (1, 'TIM2_CH2'), (5, 'SPI1_SCK'), (5, 'I2S1_CK'), (6, 'SPI3_SCK'), (6, 'I2S3_CK'), (7, 'USART1_RX'), (8, 'UART7_RX'), (9, 'I2C2_SDA'), (11, 'CAN3_RX'), ),
  ('X18', ),
  ('X19', ),
  ('X20', ),
  ('X21', (5, 'SPI2_MISO'), (6, 'I2S2_EXTSD'), ),
  ('X22', (5, 'SPI2_MOSI'), (5, 'I2S2_SD'), ),
  ('Y1', (2, 'TIM3_CH1'), (3, 'TIM8_CH1'), (5, 'I2S2_MCK'), (8, 'USART6_TX'), ),
  ('Y2', (2, 'TIM3_CH2'), (3, 'TIM8_CH2'), (5, 'SPI2_SCK'), (5, 'I2S2_CK'), (6, 'I2S3_MCK'), (8, 'USART6_RX'), ),
  ('Y3', (1, 'TIM2_CH3'), (4, 'I2C2_SCL'), (5, 'SPI2_SCK'), (5, 'I2S2_CK'), (6, 'I2S3_MCK'), (7, 'USART3_TX'), ),
  ('Y4', (2, 'TIM4_CH4'), (3, 'TIM11_CH1'), (4, 'I2C1_SDA'), (5, 'SPI2_NSS'), (5, 'I2S2_WS'), (8, 'CAN1_TX'), (9, 'I2C2_SDA'), (11, 'UART5_TX'), ),
  ('Y5', (1, 'TIM1_BKIN'), (5, 'SPI2_NSS'), (5, 'I2S2_WS'), (6, 'SPI4_NSS'), (6, 'I2S4_WS'), (7, 'SPI3_SCK'), (7, 'I2S3_CK'), (9, 'CAN2_RX'), (11, 'UART5_RX'), ),
  ('Y6', (1, 'TIM1_CH1N'), (5, 'SPI2_SCK'), (5, 'I2S2_CK'), (6, 'SPI4_SCK'), (6, 'I2S4_CK'), (8, 'USART3_CTS'), (9, 'CAN2_TX'), (11, 'UART5_TX'), ),
  ('Y7', (1, 'TIM1_CH2N'), (3, 'TIM8_CH2N'), (5, 'SPI2_MISO'), (6, 'I2S2_EXTSD'), (7, 'USART3_RTS'), (9, 'TIM12_CH1'), ),
  ('Y8', (1, 'TIM1_CH3N'), (3, 'TIM8_CH3N'), (5, 'SPI2_MOSI'), (5, 'I2S2_SD'), (9, 'TIM12_CH2'), ),
  ('Y9', (1, 'TIM1_CH1'), (4, 'I2C3_SCL'), (7, 'USART1_CK'), (8, 'UART7_RX'), (11, 'CAN3_RX'), ),
  ('Y10', (2, 'TIM4_CH3'), (3, 'TIM10_CH1'), (4, 'I2C1_SCL'), (6, 'SPI5_MOSI'), (6, 'I2S5_SD'), (8, 'CAN1_RX'), (9, 'I2C3_SDA'), (11, 'UART5_RX'), ),
  ('Y11', (1, 'TIM1_CH2N'), (2, 'TIM3_CH3'), (3, 'TIM8_CH2N'), (6, 'SPI5_SCK'), (6, 'I2S5_CK'), ),
  ('Y12', (1, 'TIM1_CH3N'), (2, 'TIM3_CH4'), (3, 'TIM8_CH3N'), (6, 'SPI5_NSS'), (6, 'I2S5_WS'), ),
  ('SW', (1, 'TIM2_CH2'), (5, 'SPI1_SCK'), (5, 'I2S1_CK'), (6, 'SPI3_SCK'), (6, 'I2S3_CK'), (7, 'USART1_RX'), (8, 'UART7_RX'), (9, 'I2C2_SDA'), (11, 'CAN3_RX'), ),
  ('LED_BLUE', (2, 'TIM3_CH2'), (5, 'SPI1_MOSI'), (5, 'I2S1_SD'), (6, 'SPI3_MOSI'), (6, 'I2S3_SD'), (9, 'CAN2_RX'), (11, 'UART5_RX'), ),
  ('LED_RED', (1, 'TIM1_CH3N'), (2, 'TIM3_CH4'), (3, 'TIM8_CH3N'), (6, 'SPI5_NSS'), (6, 'I2S5_WS'), ),
  ('LED_GREEN', (1, 'TIM1_CH2N'), (2, 'TIM3_CH3'), (3, 'TIM8_CH2N'), (6, 'SPI5_SCK'), (6, 'I2S5_CK'), ),
  ('LED_YELLOW', (2, 'TIM3_CH1'), (5, 'SPI1_MISO'), (6, 'SPI3_MISO'), (7, 'I2S3_EXTSD'), (8, 'UART7_TX'), (9, 'I2C3_SDA'), (11, 'CAN3_TX'), ),
  ('SD_D0', (2, 'TIM3_CH3'), (3, 'TIM8_CH3'), (8, 'USART6_CK'), ),
  ('SD_D1', (2, 'TIM3_CH4'), (3, 'TIM8_CH4'), (4, 'I2C3_SDA'), ),
  ('SD_D2', (6, 'SPI3_SCK'), (6, 'I2S3_CK'), (7, 'USART3_TX'), ),
  ('SD_D3', (5, 'I2S3_EXTSD'), (6, 'SPI3_MISO'), (7, 'USART3_RX'), (8, 'UART4_RX'), ),
  ('SD_CMD', (2, 'TIM3_ETR'), (8, 'UART5_RX'), ),
  ('SD_CK', (6, 'SPI3_MOSI'), (6, 'I2S3_SD'), (7, 'USART3_CK'), (8, 'UART5_TX'), ),
  ('SD_SW', (1, 'TIM2_CH1'), (1, 'TIM2_ETR'), (5, 'SPI1_NSS'), (5, 'I2S1_WS'), (6, 'SPI3_NSS'), (6, 'I2S3_WS'), (7, 'USART1_TX'), (8, 'UART7_TX'), (11, 'CAN3_TX'), ),
  ('USB_VBUS', (1, 'TIM1_CH2'), (5, 'SPI2_SCK'), (5, 'I2S2_CK'), (7, 'USART1_TX'), ),
  ('USB_DM', (1, 'TIM1_CH4'), (5, 'SPI2_NSS'), (5, 'I2S2_WS'), (6, 'SPI4_MISO'), (7, 'USART1_CTS'), (8, 'USART6_TX'), (9, 'CAN1_RX'), (11, 'UART4_RX'), ),
  ('USB_DP', (1, 'TIM1_ETR'), (5, 'SPI2_MISO'), (6, 'SPI5_MISO'), (7, 'USART1_RTS'), (8, 'USART6_RX'), (9, 'CAN1_TX'), (11, 'UART4_TX'), ),
  ('USB_ID', (1, 'TIM1_CH3'), (5, 'SPI2_MOSI'), (5, 'I2S2_SD'), (6, 'SPI5_MOSI'), (6, 'I2S5_SD'), (7, 'USART1_RX'), ),
  ('OSC32_IN', ),
  ('OSC32_OUT', ),
)
