The-Ant-Lab/arcobaleno/firmware/build-ARCOBALENO_PLUS/pins_qstr.h

Q(A0)
Q(A1)
Q(A10)
Q(A11)
Q(A12)
Q(A15)
Q(A2)
Q(A3)
Q(A4)
Q(A5)
Q(A6)
Q(A7)
Q(A8)
Q(A9)
#if defined(MICROPY_HW_CAN3_TX)
Q(AF11_CAN3)
#endif
#if defined(MICROPY_HW_UART4_TX)
Q(AF11_UART4)
#endif
#if defined(MICROPY_HW_UART5_TX)
Q(AF11_UART5)
#endif
Q(AF1_TIM1)
Q(AF1_TIM2)
Q(AF2_TIM3)
Q(AF2_TIM4)
Q(AF2_TIM5)
Q(AF3_TIM10)
Q(AF3_TIM11)
Q(AF3_TIM8)
Q(AF3_TIM9)
#if defined(MICROPY_HW_I2C1_SCL)
Q(AF4_I2C1)
#endif
#if defined(MICROPY_HW_I2C2_SCL)
Q(AF4_I2C2)
#endif
#if defined(MICROPY_HW_I2C3_SCL)
Q(AF4_I2C3)
#endif
#if (defined(MICROPY_HW_ENABLE_I2S1) && MICROPY_HW_ENABLE_I2S1)
Q(AF5_I2S1)
#endif
#if (defined(MICROPY_HW_ENABLE_I2S2) && MICROPY_HW_ENABLE_I2S2)
Q(AF5_I2S2)
#endif
#if (defined(MICROPY_HW_ENABLE_I2S3) && MICROPY_HW_ENABLE_I2S3)
Q(AF5_I2S3)
#endif
#if (defined(MICROPY_HW_ENABLE_I2S4) && MICROPY_HW_ENABLE_I2S4)
Q(AF5_I2S4)
#endif
#if defined(MICROPY_HW_SPI1_SCK)
Q(AF5_SPI1)
#endif
#if defined(MICROPY_HW_SPI2_SCK)
Q(AF5_SPI2)
#endif
#if defined(MICROPY_HW_SPI4_SCK)
Q(AF5_SPI4)
#endif
#if (defined(MICROPY_HW_ENABLE_I2S2) && MICROPY_HW_ENABLE_I2S2)
Q(AF6_I2S2)
#endif
#if (defined(MICROPY_HW_ENABLE_I2S3) && MICROPY_HW_ENABLE_I2S3)
Q(AF6_I2S3)
#endif
#if (defined(MICROPY_HW_ENABLE_I2S4) && MICROPY_HW_ENABLE_I2S4)
Q(AF6_I2S4)
#endif
#if (defined(MICROPY_HW_ENABLE_I2S5) && MICROPY_HW_ENABLE_I2S5)
Q(AF6_I2S5)
#endif
#if defined(MICROPY_HW_SPI3_SCK)
Q(AF6_SPI3)
#endif
#if defined(MICROPY_HW_SPI4_SCK)
Q(AF6_SPI4)
#endif
#if defined(MICROPY_HW_SPI5_SCK)
Q(AF6_SPI5)
#endif
#if (defined(MICROPY_HW_ENABLE_I2S3) && MICROPY_HW_ENABLE_I2S3)
Q(AF7_I2S3)
#endif
#if defined(MICROPY_HW_SPI3_SCK)
Q(AF7_SPI3)
#endif
#if defined(MICROPY_HW_UART1_TX)
Q(AF7_USART1)
#endif
#if defined(MICROPY_HW_UART2_TX)
Q(AF7_USART2)
#endif
#if defined(MICROPY_HW_UART3_TX)
Q(AF7_USART3)
#endif
#if defined(MICROPY_HW_CAN1_TX)
Q(AF8_CAN1)
#endif
#if defined(MICROPY_HW_UART4_TX)
Q(AF8_UART4)
#endif
#if defined(MICROPY_HW_UART5_TX)
Q(AF8_UART5)
#endif
#if defined(MICROPY_HW_UART7_TX)
Q(AF8_UART7)
#endif
#if defined(MICROPY_HW_UART3_TX)
Q(AF8_USART3)
#endif
#if defined(MICROPY_HW_UART6_TX)
Q(AF8_USART6)
#endif
#if defined(MICROPY_HW_CAN1_TX)
Q(AF9_CAN1)
#endif
#if defined(MICROPY_HW_CAN2_TX)
Q(AF9_CAN2)
#endif
#if defined(MICROPY_HW_I2C2_SCL)
Q(AF9_I2C2)
#endif
#if defined(MICROPY_HW_I2C3_SCL)
Q(AF9_I2C3)
#endif
Q(AF9_TIM12)
Q(AF9_TIM13)
Q(AF9_TIM14)
Q(B0)
Q(B1)
Q(B10)
Q(B12)
Q(B13)
Q(B14)
Q(B15)
Q(B3)
Q(B4)
Q(B5)
Q(B6)
Q(B7)
Q(B8)
Q(B9)
Q(C0)
Q(C1)
Q(C10)
Q(C11)
Q(C12)
Q(C13)
Q(C14)
Q(C15)
Q(C2)
Q(C3)
Q(C4)
Q(C5)
Q(C6)
Q(C7)
Q(C8)
Q(C9)
Q(D2)
Q(LED_BLUE)
Q(LED_GREEN)
Q(LED_RED)
Q(LED_YELLOW)
Q(OSC32_IN)
Q(OSC32_OUT)
Q(SD_CK)
Q(SD_CMD)
Q(SD_D0)
Q(SD_D1)
Q(SD_D2)
Q(SD_D3)
Q(SD_SW)
Q(SW)
Q(USB_DM)
Q(USB_DP)
Q(USB_ID)
Q(USB_VBUS)
Q(X1)
Q(X10)
Q(X11)
Q(X12)
Q(X17)
Q(X18)
Q(X19)
Q(X2)
Q(X20)
Q(X21)
Q(X22)
Q(X3)
Q(X4)
Q(X5)
Q(X6)
Q(X7)
Q(X8)
Q(X9)
Q(Y1)
Q(Y10)
Q(Y11)
Q(Y12)
Q(Y2)
Q(Y3)
Q(Y4)
Q(Y5)
Q(Y6)
Q(Y7)
Q(Y8)
Q(Y9)
